nurplit/bambu-lights/data/Climbing_Dot.gif

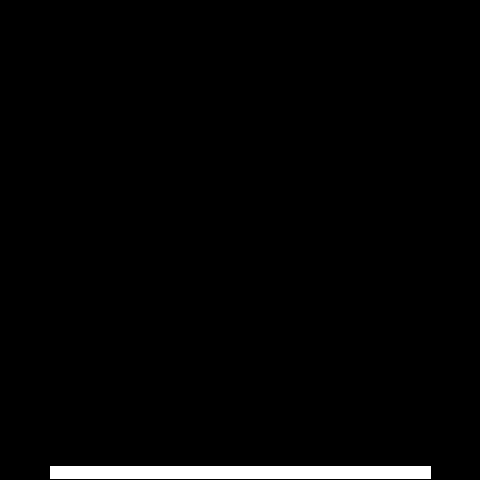
data/Climbing_Dot.gif
