nurplit/bambu-lights/data/Gradient_Fill.gif

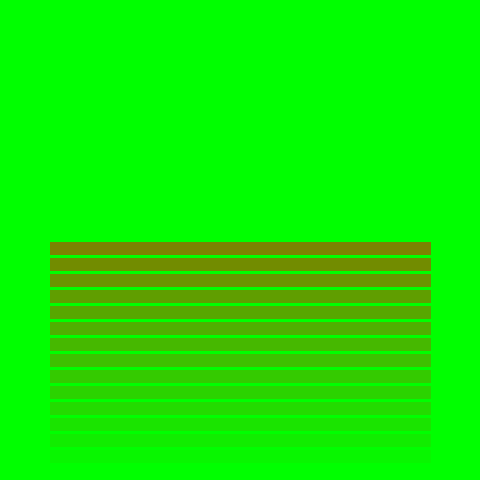
data/Gradient_Fill.gif
