nurplit/bambu-lights/src/main.cpp

/*
 * Bambu Lab Printer LED Controller
 * 
 * ESP32-based controller for addressable LED strips that displays the status
 * of Bambu Lab 3D printers via MQTT connection.
 * 
 * Inspired by and builds upon concepts from:
 * - BambuLights by judge2005 (https://github.com/judge2005/BambuLights)
 * 
 * Features:
 * - Web-based configuration interface
 * - OTA firmware updates
 * - Auto-off timer after print completion
 * - LiDAR pause support
 * - Door detection and automatic control
 * - Serial logging via web interface
 * - MQTT status monitoring
 * 
 * License: MIT
 * 
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
 * THE SOFTWARE IS PROVIDED "AS IS", WITHOUT WARRANTY OF ANY KIND, EXPRESS OR
 * IMPLIED, INCLUDING BUT NOT LIMITED TO THE WARRANTIES OF MERCHANTABILITY,
 * FITNESS FOR A PARTICULAR PURPOSE AND NONINFRINGEMENT. IN NO EVENT SHALL THE
 * AUTHORS OR COPYRIGHT HOLDERS BE LIABLE FOR ANY CLAIM, DAMAGES OR OTHER
 * LIABILITY, WHETHER IN AN ACTION OF CONTRACT, TORT OR OTHERWISE, ARISING FROM,
 * OUT OF OR IN CONNECTION WITH THE SOFTWARE OR THE USE OR OTHER DEALINGS IN THE
 * SOFTWARE.
 */

#include <Arduino.h>
#include <WiFi.h>
#include <WebServer.h>
#include <WiFiManager.h>
#include <espMqttClient.h>
#include <WiFiClientSecure.h>
#include <ArduinoJson.h>
#include <Preferences.h>
#include <ArduinoOTA.h>
#include <ESPmDNS.h>
#include <LittleFS.h>
#include "driver/rmt.h"
#include "esp_task_wdt.h"

// Custom header files
#include "config.h"
#include "structs.h"
#include "led_effects.h"
#include "printer_status.h"

// Configuration - Configurable via web interface
int led_pin = 2;                              // Default LED data pin
int num_leds = 10;                           // Default number of LEDs
String led_type = "WS2812B";                 // Default LED type
String color_order = "GRB";                  // Default color order
#define RMT_CHANNEL RMT_CHANNEL_0

// WiFi Configuration - Now handled by WiFiManager (no hardcoded credentials!)
const int WIFI_TIMEOUT_MS = 20000;           // 20 seconds timeout
WiFiManager wifiManager;                      // WiFiManager instance

// Bambu Lab MQTT Configuration - Configurable via web interface
String mqtt_server = "192.168.0.100";        // Default printer IP
int mqtt_port = 8883; // Use SSL port
const char* MQTT_USERNAME = "bblp";          // Default Bambu Lab username
String mqtt_password = "your_access_code";   // Configurable access code
String device_serial = "01S00A123456789";    // Configurable printer serial number
bool mqtt_use_ssl = true;                    // Use SSL/TLS for MQTT connection (port 8883)
bool mqtt_skip_cert_check = true;           // Skip SSL certificate verification (insecure but often needed)

// Home Assistant MQTT Configuration - Configurable via web interface
bool ha_mqtt_enabled = false;                // Enable/disable HA MQTT publishing
String ha_mqtt_server = "192.168.0.50";     // Home Assistant MQTT broker IP
int ha_mqtt_port = 1883;                    // HA MQTT broker port (usually 1883, non-SSL)
String ha_mqtt_username = "";               // HA MQTT username (empty if no auth)
String ha_mqtt_password = "";               // HA MQTT password (empty if no auth)
String ha_discovery_prefix = "homeassistant"; // HA discovery topic prefix
String ha_device_name = "Bambu Lights";     // Device name in Home Assistant
bool ha_mqtt_use_ssl = false;               // Usually false for local HA broker

// Preferences for storing settings
Preferences preferences;

// LED timing constants (in RMT ticks, 80MHz clock = 12.5ns per tick)
// Current timing values (will be set based on led_type)
int T0H = 32;   // 0 bit high time
int T0L = 64;   // 0 bit low time  
int T1H = 64;   // 1 bit high time
int T1L = 32;   // 1 bit low time

// Predefined timing for different LED types
struct LEDTiming {
    int t0h, t0l, t1h, t1l;
};

// LED type timing definitions (all in RMT ticks @ 80MHz)
const LEDTiming LED_TIMINGS[] = {
    // WS2812/WS2812B: T0H=0.4us, T0L=0.85us, T1H=0.8us, T1L=0.45us
    {32, 68, 64, 36},   // WS2812B
    // WS2811: T0H=0.5us, T0L=2.0us, T1H=1.2us, T1L=1.3us  
    {40, 160, 96, 104}, // WS2811
    // WS2813: Same as WS2812B but with backup data line
    {32, 68, 64, 36},   // WS2813
    // SK6812: T0H=0.3us, T0L=0.9us, T1H=0.6us, T1L=0.6us
    {24, 72, 48, 48},   // SK6812
    // APA102 uses SPI, but keeping for compatibility
    {32, 68, 64, 36}    // APA102 (fallback to WS2812 timing)
};

const String LED_TYPE_NAMES[] = {"WS2812B", "WS2811", "WS2813", "SK6812", "APA102"};
const String COLOR_ORDER_NAMES[] = {"RGB", "GRB", "BRG", "RBG", "GBR", "BGR"};

// Color structures (RGB defined in structs.h)
struct RGBW {
    uint8_t r, g, b, w;
};

// LED Array and RMT data (dynamically allocated in setup)
RGB* leds = nullptr;
RGBW* rgbw_leds = nullptr;
rmt_item32_t* led_data = nullptr;
bool is_rgbw = false; // Track if using RGBW LEDs

// Beacon LED Array (second strip for progress display)
RGB* beacon_leds = nullptr;
RGBW* beacon_rgbw_leds = nullptr;
rmt_item32_t* beacon_led_data = nullptr;
int beacon_led_count = DEFAULT_BEACON_LED_COUNT;
int beacon_led_pin = BEACON_LED_PIN;
int beacon_led_type = 0; // Default: WS2812B
int beacon_color_order = 1; // Default: GRB
bool beacon_enabled = false;
bool beacon_is_rgbw = false; // Track if beacon uses RGBW LEDs
String beacon_effect = "progress"; // progress, climbing, gradient, pulse
RGB beacon_color = {0, 255, 0}; // Default: green (start color for gradient)
int beacon_brightness = 80;
RGB beacon_climb_color = {255, 255, 255}; // Default: white for climbing pixel
int beacon_climb_speed = 150; // Milliseconds per step (default 150ms = 1.5s full cycle)
RGB beacon_gradient_end = {0, 0, 255}; // Default: blue for gradient end color
bool beacon_gradient_debug = false; // Flag to log gradient colors once per change
bool beacon_force_update = false; // Flag to force beacon render update

// Web Server and MQTT Client
WebServer server(80);

// Telnet Server for remote serial monitoring
WiFiServer telnetServer(23);  // Port 23 is standard for Telnet
WiFiClient telnetClient;
bool telnetConnected = false;

WiFiClient wifiClient;
WiFiClientSecure wifiClientSecure;
espMqttClientSecure mqttClient;  // Use secure client for SSL/TLS (Bambu printer)

// Home Assistant MQTT Client (separate connection)
espMqttClient haMqttClient(espMqttClientTypes::UseInternalTask::NO);

// Current mode tracking
enum LightMode {
    MODE_AUTO,      // Automatic color cycling
    MODE_MANUAL,    // Manual color control
    MODE_PRINTER,   // Bambu Lab printer status
    MODE_OFF        // LEDs off
};

LightMode currentMode = MODE_PRINTER;  // Default to Printer Status mode
RGB manualColor = {128, 0, 128}; // Default purple

// Auto-cycle fade variables
RGB currentAutoColor = {0, 0, 0};
RGB targetAutoColor = {0, 128, 0};
int fadeStep = 0;
int autoCycleSpeed = 50;  // Speed: 1-100 (higher = faster, affects FADE_STEPS)
int autoCycleBrightness = 100;  // Brightness: 0-100 (percentage)

// Printer status (struct defined in structs.h)
PrinterStatus printerStatus;

// Door event configuration
bool door_open_lights_enabled = false;
RGB door_open_color = {255, 255, 255}; // Default white for door open
bool door_is_open = false;
bool manual_door_trigger = false; // Manual override for firmware 01.10.00 bug
bool manual_beacon_trigger = false; // Manual override for beacon testing

// Timelapse configuration (uses MQTT credentials)
// printerIP comes from mqtt_server, accessCode from mqtt_password, serial from device_serial

// Auto-off timer configuration
int auto_off_minutes = 0; // 0 = disabled, otherwise minutes to wait after lights turn on
unsigned long lights_on_time = 0; // When did the lights turn on
bool auto_off_pending = false; // Is the timer running
LightMode mode_before_auto_off = MODE_PRINTER; // Remember mode to restore after auto-off

// Chamber light sync configuration
bool chamber_light_sync_enabled = true; // Sync chamber light with LED strip auto-off timer
bool chamber_light_was_on_before_auto_off = false; // Track chamber light state before auto-off

// LiDAR scanning configuration
bool lidar_lights_off_enabled = true; // Default: turn off lights during LiDAR scan
bool lidar_scanning = false;

// Printer Status LED Behavior Configuration (struct defined in structs.h)
PrinterStateBehavior behavior_heating = {"pulse", {255, 140, 0}, 70};        // Orange pulse during heating
PrinterStateBehavior behavior_printing = {"progress", {0, 255, 0}, 80};      // Green progress bar
PrinterStateBehavior behavior_idle = {"solid", {0, 0, 255}, 50};             // Blue solid
PrinterStateBehavior behavior_pause = {"solid", {255, 165, 0}, 70};          // Orange solid
PrinterStateBehavior behavior_finish = {"rainbow", {0, 0, 0}, 100};          // Rainbow cycle (color unused)
PrinterStateBehavior behavior_error = {"blink", {255, 0, 0}, 100};           // Red blink

// Track home_flag changes for debugging
long last_home_flag = 0;
bool home_flag_initialized = false;
int home_flag_update_count = 0; // Track number of updates to ensure fresh data

// MQTT Debug Logging
bool mqtt_full_logging = false; // Enable via web interface to log all MQTT traffic

// FINISH->IDLE transition control
bool idle_state_locked = false; // When true, prevent MQTT from overwriting IDLE state

// Beacon reinitialization deferred to main loop to avoid blocking web server
bool beacon_reinit_pending = false;
bool beacon_was_enabled_before_reinit = false;

// Timelapse detection
bool timelapse_active = false; // Track if timelapse is enabled for current print
bool timelapse_white_lights_enabled = true; // Force white lights during timelapse (default ON)

// Network scanning removed: user-configured manual setup via web UI is used instead.
// Keeping minimal placeholders for compatibility with older status displays.
bool scanInProgress = false;
String scanResult = "";

// Serial log buffer for web interface
#define SERIAL_LOG_SIZE 50
String serialLogs[SERIAL_LOG_SIZE];
int serialLogIndex = 0;
int serialLogCount = 0;

void addSerialLog(String msg) {
    serialLogs[serialLogIndex] = msg;
    serialLogIndex = (serialLogIndex + 1) % SERIAL_LOG_SIZE;
    if (serialLogCount < SERIAL_LOG_SIZE) {
        serialLogCount++;
    }
}

// Serial print that also logs to web interface and Telnet
void logPrint(String msg) {
    Serial.print(msg);
    addSerialLog(msg);
    // Send to Telnet client if connected
    if (telnetConnected && telnetClient && telnetClient.connected()) {
        telnetClient.print(msg);
    }
}

void logPrintln(String msg) {
    Serial.println(msg);
    addSerialLog(msg + "\n");
    // Send to Telnet client if connected
    if (telnetConnected && telnetClient && telnetClient.connected()) {
        telnetClient.println(msg);
    }
}

// Forward declarations
void updatePrinterLEDs();
void clearSettings();
void loadSettings();
void saveSettings();
bool testBambuMQTT(String ip);
void setAllLEDs(uint8_t r, uint8_t g, uint8_t b);
void clearAllLEDs();
void updateLEDs();
String listTimelapseFiles();
void publishHAState();
void publishHADiscovery();
bool connectHAMQTT();

void clearSettings() {
    preferences.begin("bambu", false);
    preferences.clear(); // Clear all saved settings
    preferences.end();
    Serial.println("EEPROM settings cleared - using defaults");
}

void loadSettings() {
    preferences.begin("bambu", false);
    mqtt_server = preferences.getString("mqtt_server", "192.168.0.100");
    mqtt_port = preferences.getInt("mqtt_port", 8883);  // Fixed default to SSL port
    mqtt_password = preferences.getString("mqtt_password", "your_access_code");
    device_serial = preferences.getString("device_serial", "01S00A123456789");
    mqtt_use_ssl = preferences.getBool("mqtt_use_ssl", true);  // Fixed default to SSL
    mqtt_skip_cert_check = preferences.getBool("mqtt_skip_cert", true);
    led_pin = preferences.getInt("led_pin", 2);
    num_leds = preferences.getInt("num_leds", 10);
    led_type = preferences.getString("led_type", "WS2812B");
    color_order = preferences.getString("color_order", "GRB");
    
    // Load door event configuration
    door_open_lights_enabled = preferences.getBool("door_lights", false);
    door_open_color.r = preferences.getUChar("door_r", 255);
    door_open_color.g = preferences.getUChar("door_g", 255);
    door_open_color.b = preferences.getUChar("door_b", 255);
    manual_door_trigger = preferences.getBool("door_trigger", false);
    // manual_beacon_trigger deliberately not loaded - always starts OFF to prevent continuous updates
    
    // Load LiDAR scanning configuration
    lidar_lights_off_enabled = preferences.getBool("lidar_lights_off", true);
    
    // Load auto-off timer configuration
    auto_off_minutes = preferences.getInt("auto_off_min", 0);
    
    // Load chamber light sync configuration
    chamber_light_sync_enabled = preferences.getBool("chamber_sync", true);
    Serial.println("Chamber Light Sync: " + String(chamber_light_sync_enabled ? "ENABLED" : "DISABLED"));
    
    // Load timelapse white lights configuration
    timelapse_white_lights_enabled = preferences.getBool("timelapse_white", true);
    Serial.println("Timelapse White Lights: " + String(timelapse_white_lights_enabled ? "ENABLED" : "DISABLED"));
    
    // Load printer status behavior settings
    behavior_heating.effect = preferences.getString("heat_effect", "pulse");
    behavior_heating.color.r = preferences.getUChar("heat_r", 255);
    behavior_heating.color.g = preferences.getUChar("heat_g", 140);
    behavior_heating.color.b = preferences.getUChar("heat_b", 0);
    behavior_heating.brightness = preferences.getInt("heat_bright", 70);
    
    behavior_printing.effect = preferences.getString("print_effect", "progress");
    behavior_printing.color.r = preferences.getUChar("print_r", 0);
    behavior_printing.color.g = preferences.getUChar("print_g", 255);
    behavior_printing.color.b = preferences.getUChar("print_b", 0);
    behavior_printing.brightness = preferences.getInt("print_bright", 80);
    
    behavior_idle.effect = preferences.getString("idle_effect", "solid");
    behavior_idle.color.r = preferences.getUChar("idle_r", 0);
    behavior_idle.color.g = preferences.getUChar("idle_g", 0);
    behavior_idle.color.b = preferences.getUChar("idle_b", 255);
    behavior_idle.brightness = preferences.getInt("idle_bright", 50);
    
    behavior_pause.effect = preferences.getString("pause_effect", "solid");
    behavior_pause.color.r = preferences.getUChar("pause_r", 255);
    behavior_pause.color.g = preferences.getUChar("pause_g", 165);
    behavior_pause.color.b = preferences.getUChar("pause_b", 0);
    behavior_pause.brightness = preferences.getInt("pause_bright", 70);
    
    behavior_finish.effect = preferences.getString("finish_effect", "rainbow");
    behavior_finish.color.r = preferences.getUChar("finish_r", 0);
    behavior_finish.color.g = preferences.getUChar("finish_g", 0);
    behavior_finish.color.b = preferences.getUChar("finish_b", 0);
    behavior_finish.brightness = preferences.getInt("finish_bright", 100);
    
    behavior_error.effect = preferences.getString("error_effect", "blink");
    behavior_error.color.r = preferences.getUChar("error_r", 255);
    behavior_error.color.g = preferences.getUChar("error_g", 0);
    behavior_error.color.b = preferences.getUChar("error_b", 0);
    behavior_error.brightness = preferences.getInt("error_bright", 100);
    
    // Load auto-cycle configuration
    autoCycleSpeed = preferences.getInt("cycle_speed", 50);
    autoCycleBrightness = preferences.getInt("cycle_bright", 100);
    
    // Load beacon LED configuration
    beacon_enabled = preferences.getBool("beacon_en", false);
    beacon_led_count = preferences.getInt("beacon_count", DEFAULT_BEACON_LED_COUNT);
    beacon_led_pin = preferences.getInt("beacon_pin", BEACON_LED_PIN);
    beacon_led_type = preferences.getInt("beacon_type", 0); // 0 = WS2812B
    beacon_color_order = preferences.getInt("beacon_order", 1); // 1 = GRB
    beacon_is_rgbw = preferences.getBool("beacon_rgbw", false); // RGB by default
    beacon_effect = preferences.getString("beacon_fx", "progress");
    beacon_color.r = preferences.getUChar("beacon_r", 0);
    beacon_color.g = preferences.getUChar("beacon_g", 255);
    beacon_color.b = preferences.getUChar("beacon_b", 0);
    beacon_brightness = preferences.getInt("beacon_bright", 80);
    beacon_climb_color.r = preferences.getUChar("beacon_climb_r", 255);
    beacon_climb_color.g = preferences.getUChar("beacon_climb_g", 255);
    beacon_climb_color.b = preferences.getUChar("beacon_climb_b", 255);
    beacon_climb_speed = preferences.getInt("bcn_clmb_spd", 150);
    beacon_gradient_end.r = preferences.getUChar("bcn_grad_end_r", 0);
    beacon_gradient_end.g = preferences.getUChar("bcn_grad_end_g", 0);
    beacon_gradient_end.b = preferences.getUChar("bcn_grad_end_b", 255);
    
    Serial.printf("Loaded beacon climb speed: %d ms\n", beacon_climb_speed);
    Serial.printf("Loaded beacon climb color: R=%d G=%d B=%d\n", beacon_climb_color.r, beacon_climb_color.g, beacon_climb_color.b);
    Serial.printf("Loaded beacon gradient end: R=%d G=%d B=%d\n", beacon_gradient_end.r, beacon_gradient_end.g, beacon_gradient_end.b);
    
    // Load Home Assistant MQTT configuration
    ha_mqtt_enabled = preferences.getBool("ha_mqtt_en", false);
    ha_mqtt_server = preferences.getString("ha_mqtt_srv", "192.168.0.50");
    ha_mqtt_port = preferences.getInt("ha_mqtt_port", 1883);
    ha_mqtt_username = preferences.getString("ha_mqtt_user", "");
    ha_mqtt_password = preferences.getString("ha_mqtt_pass", "");
    ha_discovery_prefix = preferences.getString("ha_disc_pfx", "homeassistant");
    ha_device_name = preferences.getString("ha_dev_name", "Bambu Lights");
    ha_mqtt_use_ssl = preferences.getBool("ha_mqtt_ssl", false);
    
    preferences.end();
    
    Serial.println("Settings loaded:");
    Serial.printf("MQTT Server: %s\n", mqtt_server.c_str());
    Serial.printf("MQTT Port: %d (SSL: %s)\n", mqtt_port, mqtt_use_ssl ? "YES" : "NO");
    Serial.printf("Device Serial: %s\n", device_serial.c_str());
    Serial.printf("LED Pin: %d, Count: %d\n", led_pin, num_leds);
    Serial.printf("Beacon: %s, Pin: %d, Count: %d\n", beacon_enabled ? "ENABLED" : "DISABLED", beacon_led_pin, beacon_led_count);
    Serial.printf("Door Lights: %s\n", door_open_lights_enabled ? "ENABLED" : "DISABLED");
    Serial.printf("LiDAR Lights Off: %s\n", lidar_lights_off_enabled ? "ENABLED" : "DISABLED");
    Serial.printf("Home Assistant MQTT: %s\n", ha_mqtt_enabled ? "ENABLED" : "DISABLED");
    if (ha_mqtt_enabled) {
        Serial.printf("  HA Broker: %s:%d\n", ha_mqtt_server.c_str(), ha_mqtt_port);
    }
    Serial.println("MQTT Password: [HIDDEN]");
}

void saveSettings() {
    preferences.begin("bambu", false);
    preferences.putString("mqtt_server", mqtt_server);
    preferences.putInt("mqtt_port", mqtt_port);
    preferences.putString("mqtt_password", mqtt_password);
    preferences.putString("device_serial", device_serial);
    preferences.putBool("mqtt_use_ssl", mqtt_use_ssl);
    preferences.putBool("mqtt_skip_cert", mqtt_skip_cert_check);
    preferences.putInt("led_pin", led_pin);
    preferences.putInt("num_leds", num_leds);
    preferences.putString("led_type", led_type);
    preferences.putString("color_order", color_order);
    
    // Save door event configuration
    preferences.putBool("door_lights", door_open_lights_enabled);
    preferences.putUChar("door_r", door_open_color.r);
    preferences.putUChar("door_g", door_open_color.g);
    preferences.putUChar("door_b", door_open_color.b);
    
    // Save LiDAR scanning configuration
    preferences.putBool("lidar_lights_off", lidar_lights_off_enabled);
    
    // Save chamber light sync configuration
    preferences.putBool("chamber_sync", chamber_light_sync_enabled);
    
    // Save timelapse white lights configuration
    preferences.putBool("timelapse_white", timelapse_white_lights_enabled);
    
    // Save auto-cycle configuration
    preferences.putInt("cycle_speed", autoCycleSpeed);
    preferences.putInt("cycle_bright", autoCycleBrightness);
    
    // Save beacon LED configuration
    preferences.putBool("beacon_en", beacon_enabled);
    preferences.putInt("beacon_count", beacon_led_count);
    preferences.putInt("beacon_pin", beacon_led_pin);
    preferences.putInt("beacon_type", beacon_led_type);
    preferences.putInt("beacon_order", beacon_color_order);
    preferences.putBool("beacon_rgbw", beacon_is_rgbw);
    preferences.putString("beacon_fx", beacon_effect);
    preferences.putUChar("beacon_r", beacon_color.r);
    preferences.putUChar("beacon_g", beacon_color.g);
    preferences.putUChar("beacon_b", beacon_color.b);
    preferences.putInt("beacon_bright", beacon_brightness);
    preferences.putUChar("beacon_climb_r", beacon_climb_color.r);
    preferences.putUChar("beacon_climb_g", beacon_climb_color.g);
    preferences.putUChar("beacon_climb_b", beacon_climb_color.b);
    preferences.putInt("bcn_clmb_spd", beacon_climb_speed);
    preferences.putUChar("bcn_grad_end_r", beacon_gradient_end.r);
    preferences.putUChar("bcn_grad_end_g", beacon_gradient_end.g);
    preferences.putUChar("bcn_grad_end_b", beacon_gradient_end.b);
    
    // Save Home Assistant MQTT configuration
    preferences.putBool("ha_mqtt_en", ha_mqtt_enabled);
    preferences.putString("ha_mqtt_srv", ha_mqtt_server);
    preferences.putInt("ha_mqtt_port", ha_mqtt_port);
    preferences.putString("ha_mqtt_user", ha_mqtt_username);
    preferences.putString("ha_mqtt_pass", ha_mqtt_password);
    preferences.putString("ha_disc_pfx", ha_discovery_prefix);
    preferences.putString("ha_dev_name", ha_device_name);
    preferences.putBool("ha_mqtt_ssl", ha_mqtt_use_ssl);
    
    preferences.end();
    
    Serial.println("Configuration saved to EEPROM");
}

bool testBambuMQTT(String ip) {
    Serial.printf("Testing MQTT connection to %s:%d\n", ip.c_str(), mqtt_port);
    Serial.println("Note: Using simplified test - espMqttClient conversion complete");
    
    // Simplified test - just return true since we know it's a Bambu printer
    // The full test would require setting up another espMqttClient instance
    return true; // Assume Bambu printer if IP scanning reached this point
}

// Network scanning functions removed. Manual configuration via web UI is now the supported flow.

void configureLEDTiming() {
    // Find the LED type index
    int typeIndex = 0; // Default to WS2812B
    for (int i = 0; i < 5; i++) {
        if (led_type == LED_TYPE_NAMES[i]) {
            typeIndex = i;
            break;
        }
    }
    
    // Set timing values
    T0H = LED_TIMINGS[typeIndex].t0h;
    T0L = LED_TIMINGS[typeIndex].t0l;
    T1H = LED_TIMINGS[typeIndex].t1h;
    T1L = LED_TIMINGS[typeIndex].t1l;
    
    // Check if this is an RGBW LED type
    is_rgbw = (led_type == "SK6812");
    
    // LED timing configured
}

uint32_t applyColorOrder(RGB color, uint8_t white = 0) {
    if (is_rgbw) {
        // For RGBW LEDs (SK6812), return 32-bit value with white channel
        // SK6812 standard order is GRBW (Green, Red, Blue, White)
        if (color_order == "RGBW") {
            return (color.r << 24) | (color.g << 16) | (color.b << 8) | white;
        } else if (color_order == "GRBW" || color_order == "GRB") {
            // GRB maps to GRBW for SK6812
            return (color.g << 24) | (color.r << 16) | (color.b << 8) | white;
        } else if (color_order == "RGB") {
            // RGB maps to RGBW
            return (color.r << 24) | (color.g << 16) | (color.b << 8) | white;
        } else {
            // Default: GRBW (standard SK6812 order)
            return (color.g << 24) | (color.r << 16) | (color.b << 8) | white;
        }
    } else {
        // For RGB LEDs, return 24-bit value
        if (color_order == "RGB") {
            return (color.r << 16) | (color.g << 8) | color.b;
        } else if (color_order == "GRB") {
            return (color.g << 16) | (color.r << 8) | color.b;
        } else if (color_order == "BRG") {
            return (color.b << 16) | (color.r << 8) | color.g;
        } else if (color_order == "RBG") {
            return (color.r << 16) | (color.b << 8) | color.g;
        } else if (color_order == "GBR") {
            return (color.g << 16) | (color.b << 8) | color.r;
        } else if (color_order == "BGR") {
            return (color.b << 16) | (color.g << 8) | color.r;
        }
        // Default to GRB if unknown
        return (color.g << 16) | (color.r << 8) | color.b;
    }
}

void setupRMT() {
    rmt_config_t config = {};
    config.rmt_mode = RMT_MODE_TX;
    config.channel = RMT_CHANNEL;
    config.gpio_num = (gpio_num_t)led_pin;
    config.mem_block_num = 1;
    config.clk_div = 1; // 80MHz clock
    config.tx_config.loop_en = false;
    config.tx_config.carrier_en = false;
    config.tx_config.idle_level = RMT_IDLE_LEVEL_LOW;
    config.tx_config.idle_output_en = true;
    
    ESP_ERROR_CHECK(rmt_config(&config));
    ESP_ERROR_CHECK(rmt_driver_install(config.channel, 0, 0));
}

void rgbToRMT(RGB* colors, rmt_item32_t* items, int numLeds, RGBW* rgbw_colors = nullptr) {
    int idx = 0;
    int bitsPerLed = is_rgbw ? 32 : 24; // RGBW uses 32 bits, RGB uses 24 bits
    
    for (int led = 0; led < numLeds; led++) {
        uint32_t color;
        if (is_rgbw && rgbw_colors) {
            // Use RGBW data
            RGB rgb_part = {rgbw_colors[led].r, rgbw_colors[led].g, rgbw_colors[led].b};
            color = applyColorOrder(rgb_part, rgbw_colors[led].w);
        } else {
            // Use RGB data
            color = applyColorOrder(colors[led]);
        }
        
        for (int bit = bitsPerLed - 1; bit >= 0; bit--) {
            if (color & (1UL << bit)) {
                // Send '1'
                items[idx].level0 = 1;
                items[idx].duration0 = T1H;
                items[idx].level1 = 0; 
                items[idx].duration1 = T1L;
            } else {
                // Send '0'
                items[idx].level0 = 1;
                items[idx].duration0 = T0H;
                items[idx].level1 = 0;
                items[idx].duration1 = T0L;
            }
            idx++;
        }
    }
}

void updateLEDs() {
    if (led_data) {
        if (is_rgbw && rgbw_leds) {
            rgbToRMT(nullptr, led_data, num_leds, rgbw_leds);
        } else if (leds) {
            rgbToRMT(leds, led_data, num_leds);
        }
        int bitsPerLed = is_rgbw ? 32 : 24;
        ESP_ERROR_CHECK(rmt_write_items(RMT_CHANNEL, led_data, num_leds * bitsPerLed, true));
    }
}

void setLED(int index, uint8_t r, uint8_t g, uint8_t b, uint8_t w = 0) {
    if (index >= 0 && index < num_leds) {
        if (is_rgbw && rgbw_leds) {
            // For RGBW LEDs, optimize pure white by using the white channel
            if (w == 0 && r > 0 && r == g && g == b) {
                // RGB values are equal (gray/white) - use white channel instead
                rgbw_leds[index].r = 0;
                rgbw_leds[index].g = 0;
                rgbw_leds[index].b = 0;
                rgbw_leds[index].w = r;  // Move the brightness to white channel
            } else {
                rgbw_leds[index].r = r;
                rgbw_leds[index].g = g;
                rgbw_leds[index].b = b;
                rgbw_leds[index].w = w;
            }
        } else if (leds) {
            leds[index].r = r;
            leds[index].g = g;
            leds[index].b = b;
        }
    }
}

void setAllLEDs(uint8_t r, uint8_t g, uint8_t b) {
    for (int i = 0; i < num_leds; i++) {
        setLED(i, r, g, b);
    }
}

void clearAllLEDs() {
    setAllLEDs(0, 0, 0);
}

void reallocateLEDs() {
    // Clean up existing arrays
    if (leds) {
        delete[] leds;
        leds = nullptr;
    }
    if (rgbw_leds) {
        delete[] rgbw_leds;
        rgbw_leds = nullptr;
    }
    if (led_data) {
        delete[] led_data;
        led_data = nullptr;
    }
    
    // Allocate new arrays with current num_leds
    if (num_leds > 0) {
        // Allocate RGB or RGBW array based on LED type
        if (is_rgbw) {
            rgbw_leds = new RGBW[num_leds];
            // Initialize all LEDs to off
            for (int i = 0; i < num_leds; i++) {
                rgbw_leds[i] = {0, 0, 0, 0};
            }
        } else {
            leds = new RGB[num_leds];
            // Initialize all LEDs to off
            for (int i = 0; i < num_leds; i++) {
                leds[i] = {0, 0, 0};
            }
        }
        
        // Allocate RMT data: 24 bits for RGB, 32 bits for RGBW
        int bitsPerLed = is_rgbw ? 32 : 24;
        led_data = new rmt_item32_t[num_leds * bitsPerLed];
        
        // RMT data allocated
    }
}

// ==================== BEACON LED FUNCTIONS ====================

void configureBeaconTiming() {
    // Beacon uses same timing as main LEDs, just stored separately
    // Get timing from beacon_led_type (0-4 index)
    if (beacon_led_type >= 0 && beacon_led_type < 5) {
        // Timing is already configured via LED_TIMINGS array
        // Individual beacon will use these when rendering
    }
}

void setupBeaconRMT() {
    if (!beacon_enabled || beacon_led_count <= 0) return;
    
    // Use RMT_CHANNEL_1 for beacon (main LEDs use RMT_CHANNEL_0)
    rmt_config_t config = {};
    config.rmt_mode = RMT_MODE_TX;
    config.channel = RMT_CHANNEL_1;
    config.gpio_num = (gpio_num_t)beacon_led_pin;
    config.mem_block_num = 1;
    config.clk_div = 1; // 80MHz clock
    config.tx_config.loop_en = false;
    config.tx_config.carrier_en = false;
    config.tx_config.idle_level = RMT_IDLE_LEVEL_LOW;
    config.tx_config.idle_output_en = true;
    
    esp_err_t err = rmt_config(&config);
    if (err == ESP_OK) {
        err = rmt_driver_install(config.channel, 0, 0);
        if (err == ESP_OK) {
            Serial.printf("Beacon RMT configured on GPIO %d, Channel 1\n", beacon_led_pin);
        } else {
            Serial.printf("Beacon RMT driver install failed: %d\n", err);
            beacon_enabled = false;
        }
    } else {
        Serial.printf("Beacon RMT config failed: %d\n", err);
        beacon_enabled = false;
    }
}

uint32_t applyBeaconColorOrder(RGB color) {
    // Apply color order for beacon LEDs
    switch (beacon_color_order) {
        case 0: return (color.r << 16) | (color.g << 8) | color.b; // RGB
        case 1: return (color.g << 16) | (color.r << 8) | color.b; // GRB
        case 2: return (color.b << 16) | (color.r << 8) | color.g; // BRG
        case 3: return (color.r << 16) | (color.b << 8) | color.g; // RBG
        case 4: return (color.g << 16) | (color.b << 8) | color.r; // GBR
        case 5: return (color.b << 16) | (color.g << 8) | color.r; // BGR
        default: return (color.g << 16) | (color.r << 8) | color.b; // Default GRB
    }
}

void beaconRgbToRMT(RGB* colors, rmt_item32_t* items, int numLeds) {
    int idx = 0;
    const LEDTiming& timing = LED_TIMINGS[beacon_led_type];
    int bitsPerLed = beacon_is_rgbw ? 32 : 24;
    
    for (int led = 0; led < numLeds; led++) {
        uint32_t color;
        if (beacon_is_rgbw && beacon_rgbw_leds) {
            // RGBW: send all 4 channels
            RGBW rgbw = beacon_rgbw_leds[led];
            switch (beacon_color_order) {
                case 0: color = ((uint32_t)rgbw.r << 24) | ((uint32_t)rgbw.g << 16) | ((uint32_t)rgbw.b << 8) | rgbw.w; break; // RGBW
                case 1: color = ((uint32_t)rgbw.g << 24) | ((uint32_t)rgbw.r << 16) | ((uint32_t)rgbw.b << 8) | rgbw.w; break; // GRBW
                case 2: color = ((uint32_t)rgbw.b << 24) | ((uint32_t)rgbw.r << 16) | ((uint32_t)rgbw.g << 8) | rgbw.w; break; // BRGW
                case 3: color = ((uint32_t)rgbw.r << 24) | ((uint32_t)rgbw.b << 16) | ((uint32_t)rgbw.g << 8) | rgbw.w; break; // RBGW
                case 4: color = ((uint32_t)rgbw.g << 24) | ((uint32_t)rgbw.b << 16) | ((uint32_t)rgbw.r << 8) | rgbw.w; break; // GBRW
                case 5: color = ((uint32_t)rgbw.b << 24) | ((uint32_t)rgbw.g << 16) | ((uint32_t)rgbw.r << 8) | rgbw.w; break; // BGRW
                default: color = ((uint32_t)rgbw.g << 24) | ((uint32_t)rgbw.r << 16) | ((uint32_t)rgbw.b << 8) | rgbw.w; break; // Default GRBW
            }
        } else {
            // RGB: send 3 channels
            color = applyBeaconColorOrder(colors[led]);
        }
        
        for (int bit = bitsPerLed - 1; bit >= 0; bit--) {
            if (color & (1UL << bit)) {
                items[idx].level0 = 1;
                items[idx].duration0 = timing.t1h;
                items[idx].level1 = 0;
                items[idx].duration1 = timing.t1l;
            } else {
                items[idx].level0 = 1;
                items[idx].duration0 = timing.t0h;
                items[idx].level1 = 0;
                items[idx].duration1 = timing.t0l;
            }
            idx++;
        }
    }
}

void updateBeaconLEDs() {
    if (!beacon_enabled || !beacon_leds || !beacon_led_data || beacon_led_count <= 0) {
        return;
    }
    
    // Convert LED data to RMT format
    beaconRgbToRMT(beacon_leds, beacon_led_data, beacon_led_count);
    
    // Write to RMT with NON-BLOCKING mode (wait=false) to prevent web server stalls
    // This is critical - blocking RMT writes were causing the web lockups
    int bitsPerLed = beacon_is_rgbw ? 32 : 24;
    esp_err_t err = rmt_write_items(RMT_CHANNEL_1, beacon_led_data, beacon_led_count * bitsPerLed, false);
    if (err != ESP_OK) {
        // Silently fail - don't block on errors
    }
}

void setBeaconLED(int index, uint8_t r, uint8_t g, uint8_t b) {
    if (index >= 0 && index < beacon_led_count && beacon_leds) {
        // Always set RGB values in beacon_leds (used as staging)
        beacon_leds[index].r = r;
        beacon_leds[index].g = g;
        beacon_leds[index].b = b;
        
        // Also set RGBW array if in RGBW mode
        if (beacon_is_rgbw && beacon_rgbw_leds) {
            beacon_rgbw_leds[index].r = r;
            beacon_rgbw_leds[index].g = g;
            beacon_rgbw_leds[index].b = b;
            beacon_rgbw_leds[index].w = 0; // No white channel for color LEDs
        }
    }
}

void clearBeaconLEDs() {
    for (int i = 0; i < beacon_led_count; i++) {
        setBeaconLED(i, 0, 0, 0);
    }
}

void reallocateBeaconLEDs() {
    // Clean up existing arrays
    if (beacon_leds) {
        delete[] beacon_leds;
        beacon_leds = nullptr;
    }
    if (beacon_rgbw_leds) {
        delete[] beacon_rgbw_leds;
        beacon_rgbw_leds = nullptr;
    }
    if (beacon_led_data) {
        delete[] beacon_led_data;
        beacon_led_data = nullptr;
    }
    
    // Allocate new arrays if enabled
    if (beacon_enabled && beacon_led_count > 0) {
        int bitsPerLed = beacon_is_rgbw ? 32 : 24;
        
        // Always allocate beacon_leds as staging array for RGB values
        beacon_leds = new RGB[beacon_led_count];
        for (int i = 0; i < beacon_led_count; i++) {
            beacon_leds[i] = {0, 0, 0};
        }
        
        // Additionally allocate RGBW array if needed
        if (beacon_is_rgbw) {
            beacon_rgbw_leds = new RGBW[beacon_led_count];
            for (int i = 0; i < beacon_led_count; i++) {
                beacon_rgbw_leds[i] = {0, 0, 0, 0};
            }
        }
        
        beacon_led_data = new rmt_item32_t[beacon_led_count * bitsPerLed];
        
        Serial.printf("Beacon LEDs allocated: %d LEDs (%s)\n", beacon_led_count, beacon_is_rgbw ? "RGBW" : "RGB");
    }
}

void updateBeaconProgress(int progress) {
    if (!beacon_enabled || !beacon_leds) return;
    
    // Manual override: force beacon on with current effect at 100%
    if (manual_beacon_trigger) {
        progress = 100;
    }
    
    // Skip update if progress hasn't changed (reduces CPU load significantly)
    // Exception: "progress" effect always updates for animation, or force update flag is set
    static int lastProgress = -1;
    static String lastEffect = "";
    if (progress == lastProgress && beacon_effect == lastEffect && beacon_effect != "progress" && !beacon_force_update) {
        return; // No change, skip expensive update
    }
    beacon_force_update = false; // Clear force update flag
    lastProgress = progress;
    lastEffect = beacon_effect;
    
    // Calculate brightness-adjusted color
    uint8_t r = (beacon_color.r * beacon_brightness) / 100;
    uint8_t g = (beacon_color.g * beacon_brightness) / 100;
    uint8_t b = (beacon_color.b * beacon_brightness) / 100;
    
    if (beacon_effect == "progress") {
        // Progress bar: fill from bottom to top with animated white climbing pixel
        int litLEDs = (progress * beacon_led_count) / 100;
        
        // Animated climbing pixel (continuously climbs from bottom to top)
        static unsigned long lastClimbUpdate = 0;
        static int climbPosition = 0;
        
        if (millis() - lastClimbUpdate > beacon_climb_speed) {
            lastClimbUpdate = millis();
            climbPosition++;
            if (climbPosition >= beacon_led_count) {
                climbPosition = 0; // Reset to bottom when reaching top
            }
        }
        
        // Draw progress bar
        for (int i = 0; i < beacon_led_count; i++) {
            if (i == climbPosition) {
                // Climbing pixel with custom color (always visible)
                setBeaconLED(i, beacon_climb_color.r, beacon_climb_color.g, beacon_climb_color.b);
            } else if (i < litLEDs) {
                // Normal progress color
                setBeaconLED(i, r, g, b);
            } else {
                // Off
                setBeaconLED(i, 0, 0, 0);
            }
        }
    } else if (beacon_effect == "climbing") {
        // Climbing dot: single LED moves up
        clearBeaconLEDs();
        int ledIndex = (progress * (beacon_led_count - 1)) / 100;
        setBeaconLED(ledIndex, r, g, b);
    } else if (beacon_effect == "gradient") {
        // Gradient fill: transitions from start color to end color as it fills
        uint8_t end_r = (beacon_gradient_end.r * beacon_brightness) / 100;
        uint8_t end_g = (beacon_gradient_end.g * beacon_brightness) / 100;
        uint8_t end_b = (beacon_gradient_end.b * beacon_brightness) / 100;
        
        // Log gradient colors once per change
        if (beacon_gradient_debug) {
            logPrintln("Rendering gradient: Start RGB(" + String(r) + "," + String(g) + "," + String(b) + ") -> End RGB(" + String(end_r) + "," + String(end_g) + "," + String(end_b) + ") Progress=" + String(progress) + "%");
            beacon_gradient_debug = false;
        }
        
        int litLEDs = (progress * beacon_led_count) / 100;
        for (int i = 0; i < beacon_led_count; i++) {
            if (i < litLEDs) {
                // Smooth gradient from start color (bottom) to end color (top)
                int blend = (i * 100) / max(1, litLEDs - 1);
                uint8_t grad_r = r + ((end_r - r) * blend) / 100;
                uint8_t grad_g = g + ((end_g - g) * blend) / 100;
                uint8_t grad_b = b + ((end_b - b) * blend) / 100;
                setBeaconLED(i, grad_r, grad_g, grad_b);
            } else {
                setBeaconLED(i, 0, 0, 0);
            }
        }
    } else if (beacon_effect == "pulse") {
        // Pulse: all LEDs pulse together (simplified for better performance)
        // Fill up to current progress level with pulsing brightness
        static unsigned long lastPulseCalc = 0;
        static int pulseBright = beacon_brightness;
        
        // Only recalculate pulse brightness every 100ms (was 50ms)
        if (millis() - lastPulseCalc > 100) {
            static int pulseDir = 1;
            pulseBright += pulseDir * 15;
            if (pulseBright >= beacon_brightness) {
                pulseBright = beacon_brightness;
                pulseDir = -1;
            } else if (pulseBright <= beacon_brightness / 3) {
                pulseBright = beacon_brightness / 3;
                pulseDir = 1;
            }
            lastPulseCalc = millis();
        }
        
        uint8_t pulse_r = (beacon_color.r * pulseBright) / 100;
        uint8_t pulse_g = (beacon_color.g * pulseBright) / 100;
        uint8_t pulse_b = (beacon_color.b * pulseBright) / 100;
        
        int litLEDs = (progress * beacon_led_count) / 100;
        for (int i = 0; i < beacon_led_count; i++) {
            if (i < litLEDs) {
                setBeaconLED(i, pulse_r, pulse_g, pulse_b);
            } else {
                setBeaconLED(i, 0, 0, 0);
            }
        }
    }
    
    updateBeaconLEDs();
}

// ==================== END BEACON LED FUNCTIONS ====================

bool connectWiFi() {
    logPrintln("Starting WiFi connection...");
    
    // Set blue color while connecting
    setAllLEDs(0, 0, 255);
    updateLEDs();
    
    WiFi.mode(WIFI_STA);
    
    // WiFiManager will handle the connection
    // If no saved credentials, it will start an Access Point
    wifiManager.setConfigPortalTimeout(180); // 3 minutes timeout for config portal
    wifiManager.setConnectTimeout(20);       // 20 seconds to connect to saved WiFi
    
    // Create unique AP name based on chip ID
    String apName = "BambuLED-" + String((uint32_t)ESP.getEfuseMac(), HEX);
    logPrintln("AP Name (if needed): " + apName);
    logPrintln("If no WiFi configured, connect to AP and visit 192.168.4.1");
    
    // Blink blue while connecting
    bool ledState = false;
    wifiManager.setAPCallback([](WiFiManager *myWiFiManager) {
        Serial.println("Entered config mode - AP started");
        Serial.println("Connect to: " + String(myWiFiManager->getConfigPortalSSID()));
        Serial.println("Visit: 192.168.4.1 to configure WiFi");
    });
    
    // Try to connect with saved credentials or start config portal
    bool connected = wifiManager.autoConnect(apName.c_str());
    
    if (connected) {
        logPrintln("WiFi connected! IP: " + WiFi.localIP().toString());
        logPrintln("Signal strength: " + String(WiFi.RSSI()) + " dBm");
        
        // Green color for successful connection
        setAllLEDs(0, 255, 0);
        updateLEDs();
        delay(2000);
        
        return true;
    } else {
        logPrintln("WiFi connection failed or timed out!");
        
        // Red color for failed connection
        setAllLEDs(255, 0, 0);
        updateLEDs();
        delay(2000);
        
        return false;
    }
}

// MQTT Functions
static unsigned long messageCount = 0;
static String assembledMessage = "";
static String assembledTopic = "";

// Forward declaration
void processMqttMessage(const String& topic, const String& message);

// Send MQTT command to printer
void sendPrinterCommand(const String& command) {
    if (!mqttClient.connected()) {
        logPrintln("Cannot send command - MQTT not connected");
        return;
    }
    
    String requestTopic = "device/" + device_serial + "/request";
    logPrintln("Sending MQTT command to: " + requestTopic);
    logPrintln("Command: " + command);
    
    mqttClient.publish(requestTopic.c_str(), 0, false, command.c_str());
}

// Control chamber light (on/off with optional brightness)
void setChamberLight(bool on, int brightness = 100) {
    // Track last command to avoid flooding MQTT with redundant messages
    static bool last_state = false;
    static unsigned long last_command_time = 0;
    static uint32_t seq_id = 1;
    unsigned long now = millis();
    
    // Only send if state changed OR it's been more than 5 seconds (for reliability)
    if (on == last_state && (now - last_command_time < 5000)) {
        return; // Skip redundant command
    }
    
    last_state = on;
    last_command_time = now;
    
    // Try direct LED mode control for chamber light
    // Mode: "on" or "off" for chamber light control
    String command = "{\"system\":{\"sequence_id\":\"" + String(seq_id++) + 
                     "\",\"command\":\"ledctrl\",\"led_node\":\"chamber_light\",\"led_mode\":\"";
    command += on ? "on" : "off";
    command += "\",\"led_on_time\":500,\"led_off_time\":500,\"loop_times\":1,\"interval_time\":0}}";
    
    sendPrinterCommand(command);
    logPrintln("Chamber light: " + String(on ? "ON" : "OFF") + " (LED control: " + String(on ? "on" : "off") + ")");
}

void onMqttMessage(const espMqttClientTypes::MessageProperties& properties, const char* topic, const uint8_t* payload, size_t len, size_t index, size_t total) {
    // Handle message assembly for multi-part messages
    if (index == 0) {
        // Start of new message
        messageCount++;
        assembledMessage = "";
        assembledTopic = String(topic);
        if (messageCount % 10 == 1) { // Log every 10th message to web
            logPrintln("MQTT message #" + String(messageCount) + " (" + String(total) + " bytes)");
        }
    }
    
    // Append this part to the assembled message
    for (size_t i = 0; i < len; i++) {
        assembledMessage += (char)payload[i];
    }
    
    // Only process when we have the complete message (index + len == total)
    if (index + len >= total) {

        
        processMqttMessage(assembledTopic, assembledMessage);
    }
}

void processMqttMessage(const String& topic, const String& message) {
    // Throttle message processing to avoid blocking web server
    static unsigned long lastProcessTime = 0;
    unsigned long now = millis();
    
    // Process at most once per 100ms to keep web responsive
    if (now - lastProcessTime < 100) {
        return; // Skip this message, too soon after last one
    }
    lastProcessTime = now;
    
    yield(); // Yield before heavy processing
    
    // Full MQTT logging if enabled
    if (mqtt_full_logging) {
        logPrintln("========== MQTT MESSAGE ==========");
        logPrintln("Topic: " + topic);
        logPrintln("Size: " + String(message.length()) + " bytes");
        logPrintln("Payload: " + message);
        logPrintln("==================================");
    }
    
    // Parse JSON message - 20KB buffer needed for large Bambu Lab messages
    DynamicJsonDocument doc(20480); // 20KB buffer for 15.6KB messages
    DeserializationError error = deserializeJson(doc, message);
    
    yield(); // Yield after heavy JSON parsing
    
    if (error) {
        Serial.printf("JSON error: %s\n", error.c_str());
        return;
    }
    
    // Update printer status
    printerStatus.online = true;
    printerStatus.lastUpdate = millis();
    
    // Log key fields for debugging (always enabled for state tracking)
    if (doc.containsKey("print")) {
        JsonObject print = doc["print"];
        String debugInfo = "MQTT Update: ";
        
        if (print.containsKey("gcode_state")) {
            debugInfo += "State=" + print["gcode_state"].as<String>() + " ";
        }
        if (print.containsKey("mc_print_stage")) {
            debugInfo += "Stage=" + print["mc_print_stage"].as<String>() + " ";
        }
        if (print.containsKey("stg_cur")) {
            debugInfo += "StgNum=" + String(print["stg_cur"].as<int>()) + " ";
        }
        if (print.containsKey("mc_percent")) {
            debugInfo += "Progress=" + String(print["mc_percent"].as<int>()) + "% ";
        }
        if (print.containsKey("layer_num")) {
            debugInfo += "Layer=" + String(print["layer_num"].as<int>());
            if (print.containsKey("total_layer_num")) {
                debugInfo += "/" + String(print["total_layer_num"].as<int>());
            }
            debugInfo += " ";
        }
        if (print.containsKey("bed_temper")) {
            debugInfo += "Bed=" + String(print["bed_temper"].as<float>(), 1) + "C ";
        }
        if (print.containsKey("nozzle_temper")) {
            debugInfo += "Nozzle=" + String(print["nozzle_temper"].as<float>(), 1) + "C ";
        }
        
        // Only show error code if non-zero (indicates actual error)
        if (print.containsKey("print_error")) {
            int error_code = print["print_error"].as<int>();
            if (error_code != 0) {
                debugInfo += "Error=" + String(error_code) + " ";
            }
        }
        
        if (debugInfo.length() > 13) { // More than just "MQTT Update: "
            logPrintln(debugInfo);
        }
    }
    
    if (doc.containsKey("print")) {
        JsonObject print = doc["print"];
        
        // Parse stage - try multiple field names
        if (print.containsKey("stg_cur")) {
            // stg_cur is the actual stage number (more reliable)
            int stage_num = print["stg_cur"];
            printerStatus.stage = String(stage_num);
        } else if (print.containsKey("stage")) {
            printerStatus.stage = print["stage"].as<String>();
        }
        
        if (print.containsKey("mc_percent")) {
            printerStatus.progress = print["mc_percent"];
        }
        
        // Check for timelapse mode in ipcam object
        if (print.containsKey("ipcam")) {
            JsonObject ipcam = print["ipcam"];
            if (ipcam.containsKey("timelapse")) {
                String timelapse_str = ipcam["timelapse"].as<String>();
                bool new_timelapse_state = (timelapse_str == "enable");
                
                // Log timelapse state changes
                if (new_timelapse_state != timelapse_active) {
                    logPrintln("=== TIMELAPSE STATE CHANGE ===");
                    logPrintln("Timelapse: " + String(timelapse_active ? "ON" : "OFF") + " -> " + String(new_timelapse_state ? "ON" : "OFF"));
                    logPrintln("============================");
                    timelapse_active = new_timelapse_state;
                }
            }
        }
        
        if (print.containsKey("gcode_state")) {
            String old_state = printerStatus.gcode_state;
            String new_state = print["gcode_state"].as<String>();
            
            // If a new print starts (RUNNING/PREPARE), unlock the idle state
            if (new_state == "RUNNING" || new_state == "PREPARE") {
                idle_state_locked = false;
            }
            
            // Only update gcode_state if not locked in IDLE
            if (!idle_state_locked) {
                printerStatus.gcode_state = new_state;
            }
            
            // Log print state changes
            if (old_state != printerStatus.gcode_state) {
                logPrintln("=== PRINT STATE CHANGE ===");
                logPrintln("From: " + old_state + " -> To: " + printerStatus.gcode_state);
                logPrintln("Progress: " + String(printerStatus.progress) + "%");
                logPrintln("Layer: " + String(printerStatus.layer_num) + "/" + String(printerStatus.total_layer_num));
                logPrintln("========================");
            }
            
            // Clear timelapse state when print ends
            if ((printerStatus.gcode_state == "FINISH" || printerStatus.gcode_state == "IDLE") && timelapse_active) {
                logPrintln("Print ended - clearing timelapse state");
                timelapse_active = false;
            }
            
            // Cancel auto-off timer when a new print starts (RUNNING or PREPARE state)
            if ((printerStatus.gcode_state == "RUNNING" || printerStatus.gcode_state == "PREPARE") && 
                (old_state != "RUNNING" && old_state != "PREPARE") && auto_off_pending) {
                auto_off_pending = false;
                logPrintln("Auto-off timer cancelled: New print started");
            }
            
            // Start auto-off timer when print finishes (if in PRINTER mode and timer enabled)
            if (printerStatus.gcode_state == "FINISH" && old_state != "FINISH" && 
                auto_off_minutes > 0 && !auto_off_pending && currentMode == MODE_PRINTER) {
                auto_off_pending = true;
                lights_on_time = millis();
                logPrintln("Print complete - auto-off timer started: " + String(auto_off_minutes) + " minutes");
            }
        }
        
        // mc_print_stage is usually a string like "printing", "heating", etc.
        if (print.containsKey("mc_print_stage")) {
            printerStatus.mc_print_stage = print["mc_print_stage"].as<String>();
        }
        
        // print_real_action is usually a numeric code
        if (print.containsKey("print_real_action")) {
            printerStatus.print_real_action = String(print["print_real_action"].as<int>());
        }
        
        // Get layer information for first layer detection
        if (print.containsKey("layer_num")) {
            printerStatus.layer_num = print["layer_num"];
        }
        if (print.containsKey("total_layer_num")) {
            printerStatus.total_layer_num = print["total_layer_num"];
        }
        
        yield(); // Yield during processing
        
        // Capture additional fields to detect true idle state
        if (print.containsKey("gcode_file")) {
            printerStatus.gcode_file = print["gcode_file"].as<String>();
        }
        if (print.containsKey("subtask_name")) {
            printerStatus.subtask_name = print["subtask_name"].as<String>();
        }
        if (print.containsKey("print_error")) {
            printerStatus.print_error = print["print_error"];
        }
        
        yield(); // Yield after field extraction
        
        // Smart FINISH->IDLE and FAILED->IDLE transition using mc_print_stage
        // mc_print_stage: 1 = idle/no active print, 2 = printing/preparing
        // When printer is in FINISH/FAILED state but mc_print_stage returns to 1, it's truly idle
        if ((printerStatus.gcode_state == "FINISH" || printerStatus.gcode_state == "FAILED") && 
            printerStatus.mc_print_stage == "1" && 
            !idle_state_locked) {
            logPrintln("=== AUTO IDLE DETECTION ===");
            logPrintln(printerStatus.gcode_state + " state with Print Stage=1 (no active job) - transitioning to IDLE");
            logPrintln("Progress: " + String(printerStatus.progress) + "%, Layer: " + String(printerStatus.layer_num) + "/" + String(printerStatus.total_layer_num));
            logPrintln("Locking IDLE state to prevent MQTT overwrite");
            logPrintln("=========================");
            printerStatus.gcode_state = "IDLE";
            idle_state_locked = true; // Lock IDLE state until next print starts
        }
    }
    
    // Parse temperature data - handle multiple field name variations
    if (doc.containsKey("print")) {
        JsonObject print = doc["print"];
        
        // Bed temperature - actual current temperature
        if (print.containsKey("bed_temper")) {
            printerStatus.bed_temp = print["bed_temper"].as<float>();
            logPrintln("Bed temp from print.bed_temper: " + String(printerStatus.bed_temp));
        }
        
        // Nozzle temperature - actual current temperature
        if (print.containsKey("nozzle_temper")) {
            printerStatus.nozzle_temp = print["nozzle_temper"].as<float>();
            logPrintln("Nozzle temp from print.nozzle_temper: " + String(printerStatus.nozzle_temp));
        }
    }
    
    // Legacy support for temp object (if it exists in some firmware versions)
    if (doc.containsKey("temp")) {
        JsonObject temp = doc["temp"];
        if (temp.containsKey("bed_temper") && printerStatus.bed_temp == 0.0) {
            printerStatus.bed_temp = temp["bed_temper"].as<float>();
        }
        if (temp.containsKey("nozzle_temper") && printerStatus.nozzle_temp == 0.0) {
            printerStatus.nozzle_temp = temp["nozzle_temper"].as<float>();
        }
    }
    
    // Show key printer status when available with temperature info
    if (doc.containsKey("print")) {
        JsonObject print = doc["print"];
        if (print.containsKey("gcode_state")) {
            Serial.printf("State: %s", print["gcode_state"].as<String>().c_str());
        }
        if (print.containsKey("layer_num") && print.containsKey("total_layer_num")) {
            Serial.printf(", Layer: %d/%d", print["layer_num"].as<int>(), print["total_layer_num"].as<int>());
        }
        if (print.containsKey("mc_print_stage")) {
            Serial.printf(", Stage: %s", print["mc_print_stage"].as<String>().c_str());
        }
        if (print.containsKey("stg_cur")) {
            Serial.printf(", StgCur: %d", print["stg_cur"].as<int>());
        }
        Serial.println();
    }
    
    // Show temperature data when available
    if (doc.containsKey("temp")) {
        JsonObject temp = doc["temp"];
        bool has_temp = false;
        if (temp.containsKey("bed_temper") || temp.containsKey("bed_temp")) {
            Serial.printf("Temps: Bed=%.1f°C", printerStatus.bed_temp);
            has_temp = true;
        }
        if (temp.containsKey("nozzle_temper") || temp.containsKey("nozzle_temp")) {
            if (has_temp) Serial.printf(", ");
            else Serial.printf("Temps: ");
            Serial.printf("Nozzle=%.1f°C", printerStatus.nozzle_temp);
            has_temp = true;
        }
        if (has_temp) Serial.println();
    }
    
    // Check for door events using proper bit 23 (0x00800000) detection
    // Note: Don't reset door_detected here - it's a global variable that should maintain state between messages
    // Only update it when home_flag is actually present in the MQTT message
    static bool door_detected = false;
    
    // Primary method: Check bit 23 in home_flag (standard Bambu Lab door sensor bit)
    // home_flag is typically inside the "print" object
    if (doc.containsKey("print") && doc["print"].containsKey("home_flag")) {
        long home_flag = doc["print"]["home_flag"];
        
        // Track home_flag changes for door detection
        if (!home_flag_initialized || home_flag != last_home_flag) {
            if (!home_flag_initialized) {
                Serial.printf("Home flag initialized: 0x%08X\n", (unsigned long)home_flag);
                home_flag_initialized = true;
            } else {
                // Check specifically bit 23 (door bit)
                unsigned long old_unsigned = (unsigned long)last_home_flag;
                unsigned long new_unsigned = (unsigned long)home_flag;
                bool old_door_bit = (old_unsigned & 0x00800000UL) != 0;
                bool new_door_bit = (new_unsigned & 0x00800000UL) != 0;
                if (old_door_bit != new_door_bit) {
                    Serial.printf("DOOR %s (home_flag: 0x%08X)\n",
                                 new_door_bit ? "OPENED" : "CLOSED", new_unsigned);
                }
            }
            last_home_flag = home_flag;
        }
        
        const unsigned long DOOR_OPEN_BIT = 0x00800000UL; // Bit 23 (24th bit, zero-indexed)
        
        // Convert to unsigned for proper bit operations
        unsigned long home_flag_unsigned = (unsigned long)home_flag;
        
        // Update door_detected based on bit state
        door_detected = (home_flag_unsigned & DOOR_OPEN_BIT) != 0;
    } else if (doc.containsKey("home_flag")) {
        // Fallback: check at root level
        long home_flag = doc["home_flag"];
        
        // Track root level home_flag changes
        if (!home_flag_initialized || home_flag != last_home_flag) {
            if (!home_flag_initialized) {
                Serial.printf("Home flag initialized (root): 0x%08X - Waiting for fresh update...\n", (unsigned long)home_flag);
                home_flag_initialized = true;
            } else {
                // This is a REAL update (not first stale value)
                home_flag_update_count++;
                
                // Check door bit changes (bit 23: 1=CLOSED, 0=OPEN - inverted logic)
                unsigned long old_unsigned = (unsigned long)last_home_flag;
                unsigned long new_unsigned = (unsigned long)home_flag;
                bool old_door_bit = (old_unsigned & 0x00800000UL) != 0;
                bool new_door_bit = (new_unsigned & 0x00800000UL) != 0;
                if (old_door_bit != new_door_bit) {
                    // Inverted: bit SET = CLOSED, bit CLEAR = OPEN
                    Serial.printf("DOOR %s (home_flag: 0x%08X)\n",
                                 new_door_bit ? "CLOSED" : "OPENED", new_unsigned);
                }
            }
            last_home_flag = home_flag;
        }
        
        // Only trust door detection after we've received at least one real update
        if (home_flag_update_count > 0) {
            const unsigned long DOOR_CLOSED_BIT = 0x00800000UL;  // Bit 23: 1=CLOSED, 0=OPEN
            unsigned long home_flag_unsigned = (unsigned long)home_flag;
            
            // Update door_detected: Door is OPEN when bit is CLEAR (inverted logic)
            door_detected = !(home_flag_unsigned & DOOR_CLOSED_BIT);
        }
    }
    
    // Combine automatic detection with manual trigger
    bool prev_door_state = door_is_open;
    door_is_open = door_detected || manual_door_trigger;
    bool door_just_closed = prev_door_state && !door_is_open;
    
    // Log door state changes with detailed info
    if (door_is_open != prev_door_state) {
        String doorSource = "";
        if (door_detected && manual_door_trigger) {
            doorSource = " (Auto + Manual)";
        } else if (door_detected) {
            doorSource = " (Auto Detection)";
        } else if (manual_door_trigger) {
            doorSource = " (Manual Override)";
        }
        
        logPrintln("=== DOOR STATE CHANGE ===" + doorSource);
        logPrintln("Door: " + String(door_is_open ? "OPEN" : "CLOSED"));
        logPrintln("Door Lights Enabled: " + String(door_open_lights_enabled ? "YES" : "NO"));
        logPrintln("Current Mode: " + String(
            currentMode == MODE_AUTO ? "AUTO" :
            currentMode == MODE_MANUAL ? "MANUAL" :
            currentMode == MODE_PRINTER ? "PRINTER" : "OFF"
        ));
        
        // If door opens and mode is OFF (from auto-off), restore previous mode
        if (door_is_open && currentMode == MODE_OFF && door_open_lights_enabled) {
            logPrintln("Restoring mode from AUTO-OFF: " + String(
                mode_before_auto_off == MODE_AUTO ? "AUTO" :
                mode_before_auto_off == MODE_MANUAL ? "MANUAL" :
                mode_before_auto_off == MODE_PRINTER ? "PRINTER" : "OFF"
            ));
            currentMode = mode_before_auto_off;
            
            // Restore chamber light if it was on before auto-off
            if (chamber_light_sync_enabled && chamber_light_was_on_before_auto_off && mqttClient.connected()) {
                logPrintln("Restoring chamber light (synced)");
                setChamberLight(true);
                chamber_light_was_on_before_auto_off = false;
            }
        }
        
        logPrintln("========================");
    }
    
    // Transition from FINISHED to IDLE when door closes (after user retrieves print)
    if (!door_is_open && prev_door_state && printerStatus.gcode_state == "FINISH") {
        logPrintln("=== PRINT RETRIEVED ===");
        logPrintln("Door closed after FINISH state - transitioning to IDLE");
        printerStatus.gcode_state = "IDLE";
        logPrintln("======================");
    }
    
    // Start auto-off timer if door opens and lights turn on (if timer enabled and not already running)
    if (door_is_open && !prev_door_state && auto_off_minutes > 0 && 
        currentMode == MODE_PRINTER && door_open_lights_enabled) {
        if (!auto_off_pending) {
            auto_off_pending = true;
            lights_on_time = millis();
            logPrintln("Door opened - auto-off timer started: " + String(auto_off_minutes) + " minutes");
        } else {
            // If timer already running, restart it
            lights_on_time = millis();
            logPrintln("Door opened - auto-off timer restarted");
        }
    }
    
    // *** LiDAR SCANNING DETECTION ***
    // Detect when the printer is performing LiDAR scans (typically after first layer)
    bool new_lidar_scanning = false;
    
    // Check for LiDAR scanning conditions
    if (printerStatus.mc_print_stage == "scanning" || 
        printerStatus.mc_print_stage == "first_layer_scan" ||
        printerStatus.mc_print_stage == "auto_bed_leveling" ||
        printerStatus.print_real_action == "scanning" ||
        printerStatus.print_real_action == "lidar_scan" ||
        printerStatus.print_real_action == "first_layer_inspect" ||
        (printerStatus.layer_num == 1 && 
         (printerStatus.mc_print_stage.indexOf("inspect") >= 0 || 
          printerStatus.mc_print_stage.indexOf("scan") >= 0)) ||
        printerStatus.mc_print_stage.indexOf("bed_leveling") >= 0 ||
        printerStatus.mc_print_stage.indexOf("calibrat") >= 0 ||
        printerStatus.print_real_action.indexOf("bed_leveling") >= 0 ||
        printerStatus.print_real_action.indexOf("calibrat") >= 0) {
        new_lidar_scanning = true;
    }
    
    // Update LiDAR scanning state
    if (new_lidar_scanning != lidar_scanning) {
        lidar_scanning = new_lidar_scanning;
        if (lidar_scanning) {
            logPrintln("=== LiDAR SCAN STARTED ===");
            logPrintln("Stage: " + printerStatus.mc_print_stage);
            logPrintln("Action: " + printerStatus.print_real_action);
            logPrintln("Layer: " + String(printerStatus.layer_num));
            logPrintln("Lights: " + String(lidar_lights_off_enabled ? "OFF (pause enabled)" : "STAYING ON (pause disabled)"));
            logPrintln("========================");
        } else {
            logPrintln("=== LiDAR SCAN ENDED - Lights Restored ===");
        }
    }
    
    yield(); // Final yield before LED update
    
    // Only update LEDs based on printer state if in PRINTER mode
    // Skip updates when door is open (to prevent jogging from changing LED color)
    // Force update when door closes to immediately restore LEDs to printer state
    if (currentMode == MODE_PRINTER && (!door_is_open || door_just_closed)) {
        updatePrinterLEDs();
    }
    
    yield(); // Yield after processing complete
}

// Apply LED effect based on behavior configuration (declaration in led_effects.h)
void applyEffect(PrinterStateBehavior& behavior, int progress) {
    uint8_t r = (behavior.color.r * behavior.brightness) / 100;
    uint8_t g = (behavior.color.g * behavior.brightness) / 100;
    uint8_t b = (behavior.color.b * behavior.brightness) / 100;
    
    if (behavior.effect == "solid") {
        setAllLEDs(r, g, b);
    } 
    else if (behavior.effect == "blink") {
        static unsigned long lastBlink = 0;
        static bool blinkState = false;
        if (millis() - lastBlink > 500) {
            blinkState = !blinkState;
            lastBlink = millis();
        }
        if (blinkState) {
            setAllLEDs(r, g, b);
        } else {
            clearAllLEDs();
        }
    }
    else if (behavior.effect == "breathe") {
        static unsigned long lastBreath = 0;
        static float breathPhase = 0;
        if (millis() - lastBreath > 30) {
            breathPhase += 0.05;
            if (breathPhase > 6.28) breathPhase = 0;
            lastBreath = millis();
        }
        float brightness = (sin(breathPhase) + 1.0) / 2.0;  // 0.0 to 1.0
        setAllLEDs(r * brightness, g * brightness, b * brightness);
    }
    else if (behavior.effect == "pulse") {
        static unsigned long lastPulse = 0;
        static bool pulseOn = false;
        static float pulsePhase = 0;
        
        if (pulseOn) {
            // Quick fade in/out pulse
            if (millis() - lastPulse > 15) {
                pulsePhase += 0.15;
                if (pulsePhase > 3.14) {  // Half sine wave (0 to π)
                    pulsePhase = 0;
                    pulseOn = false;
                    lastPulse = millis();
                }
            }
            float brightness = sin(pulsePhase);  // 0.0 to 1.0
            setAllLEDs(r * brightness, g * brightness, b * brightness);
        } else {
            // Off period between pulses
            setAllLEDs(0, 0, 0);
            if (millis() - lastPulse > 1500) {  // 1.5 second pause between pulses
                pulseOn = true;
                pulsePhase = 0;
                lastPulse = millis();
            }
        }
    }
    else if (behavior.effect == "progress" && progress >= 0) {
        // Progress bar effect
        if (progress < 0) progress = 0;
        if (progress > 100) progress = 100;
        
        int ledsToLight = (progress * num_leds) / 100;
        clearAllLEDs();
        
        // Light up completed portion
        for (int i = 0; i < ledsToLight && i < num_leds; i++) {
            setLED(i, r, g, b);
        }
        
        // Show leading edge in brighter color
        if (progress >= 1 && progress < 100 && ledsToLight < num_leds) {
            setLED(ledsToLight, behavior.color.r, behavior.color.g, behavior.color.b);  // Full brightness leading edge
        }
    }
    else if (behavior.effect == "rainbow") {
        // Rainbow cycle effect
        static unsigned long lastRainbow = 0;
        static int rainbowOffset = 0;
        if (millis() - lastRainbow > 50) {  // Update every 50ms
            rainbowOffset = (rainbowOffset + 1) % 256;
            lastRainbow = millis();
        }
        
        for (int i = 0; i < num_leds; i++) {
            int hue = (rainbowOffset + (i * 256 / num_leds)) % 256;
            
            // HSV to RGB conversion (simplified)
            int segment = hue / 43;  // 0-5
            int fraction = (hue % 43) * 6;  // 0-255
            
            int p = 0;
            int q = (255 * (255 - fraction)) / 255;
            int t = (255 * fraction) / 255;
            
            int rr, gg, bb;
            switch(segment) {
                case 0: rr = 255; gg = t;   bb = p;   break;
                case 1: rr = q;   gg = 255; bb = p;   break;
                case 2: rr = p;   gg = 255; bb = t;   break;
                case 3: rr = p;   gg = q;   bb = 255; break;
                case 4: rr = t;   gg = p;   bb = 255; break;
                default: rr = 255; gg = p;   bb = q;   break;
            }
            
            // Apply brightness scaling
            rr = (rr * behavior.brightness) / 100;
            gg = (gg * behavior.brightness) / 100;
            bb = (bb * behavior.brightness) / 100;
            
            setLED(i, rr, gg, bb);
        }
    }
    else {
        // Default to solid if unknown effect
        setAllLEDs(r, g, b);
    }
}

void updatePrinterLEDs() {
    if (currentMode != MODE_PRINTER) return;
    
    // Door open has priority - skip printer LED updates when door is open
    // IMPORTANT: This prevents LED state from updating, but door lights handle the override
    if (door_open_lights_enabled && door_is_open) {
        // Don't return immediately - let door lights in main loop handle this
        // This prevents state from getting stuck when door closes
        return;
    }
    
    // Priority 1: LiDAR scanning - turn off lights to avoid interference (if enabled)
    if (lidar_lights_off_enabled && lidar_scanning) {
        clearAllLEDs();
        updateLEDs();
        return;
    }
    
    // Track LED mode for change detection
    static uint8_t last_led_mode = 0; // 0=none, 1=white, 2=normal
    static String last_gcode_state = "";
    static bool finish_effect_logged = false;
    uint8_t current_led_mode = 0;
    
    // Log state changes for debugging
    if (printerStatus.gcode_state != last_gcode_state) {
        logPrintln(">>> PRINTER STATE CHANGE: " + last_gcode_state + " -> " + printerStatus.gcode_state + " <<<");
        last_gcode_state = printerStatus.gcode_state;
        finish_effect_logged = false; // Reset when state changes
        
        // Publish state change to Home Assistant
        publishHAState();
    }
    
    // Priority 2: Timelapse mode - force white lights during printing for consistent lighting
    // Only activate if BOTH the setting is enabled AND timelapse is actually active in the print
    if (timelapse_white_lights_enabled && timelapse_active && (printerStatus.gcode_state == "RUNNING" || printerStatus.gcode_state == "PREPARE")) {
        current_led_mode = 1; // White mode
        if (last_led_mode != 1) {
            logPrintln(">>> LED MODE CHANGE: Timelapse WHITE lights active <<<");
            last_led_mode = 1;
        }
        
        setAllLEDs(255, 255, 255); // Full white for timelapse
        updateLEDs();
        
        // Keep chamber light on if sync is enabled (always on for timelapse white mode)
        if (chamber_light_sync_enabled) {
            setChamberLight(true);
        }
        
        // Prevent auto-off during timelapse recording
        if (auto_off_pending) {
            auto_off_pending = false;
            logPrintln("Auto-off cancelled: Timelapse recording active");
        }
        
        return;
    }
    
    // Handle timelapse active but white lights disabled - keep chamber on only if using white printing color
    if (timelapse_active && (printerStatus.gcode_state == "RUNNING" || printerStatus.gcode_state == "PREPARE")) {
        current_led_mode = 2; // Normal mode
        if (last_led_mode != 2) {
            logPrintln(">>> LED MODE CHANGE: Timelapse NORMAL lights (using printer status colors) <<<");
            last_led_mode = 2;
        }
        
        // Keep chamber light on if sync is enabled AND printing color is white (255,255,255)
        // This prevents chamber light from washing out custom printing colors
        if (chamber_light_sync_enabled && 
            behavior_printing.color.r == 255 && 
            behavior_printing.color.g == 255 && 
            behavior_printing.color.b == 255) {
            setChamberLight(true);
        }
        
        // Prevent auto-off during timelapse recording
        if (auto_off_pending) {
            auto_off_pending = false;
            logPrintln("Auto-off cancelled: Timelapse recording active (white lights disabled)");
        }
        // Continue to normal printer status logic below
    }
    
    // If we're no longer in timelapse mode, reset tracking
    if (current_led_mode == 0 && last_led_mode != 0) {
        logPrintln(">>> LED MODE CHANGE: Exited timelapse mode <<<");
        last_led_mode = 0;
    }
    
    // Priority 3: Printer state-based colors with configurable effects
    if (!printerStatus.online || millis() - printerStatus.lastUpdate > 60000) {
        // Offline/Error - use error behavior
        applyEffect(behavior_error);
    } else if (printerStatus.gcode_state == "IDLE") {
        applyEffect(behavior_idle);
    } else if (printerStatus.gcode_state == "RUNNING" || printerStatus.gcode_state == "PREPARE") {
        // Check stage number to differentiate heating from actual printing
        // Stage 2 = HEATBED_PREHEATING, Stage 3 = HEATING_HOTEND, etc.
        // Stage 14+ = actual printing stages
        int stageNum = printerStatus.stage.toInt();
        if (stageNum > 0 && stageNum < 10 && printerStatus.progress == 0) {
            // Heating/preparation stages (stage 1-9) with 0% progress = heating phase
            applyEffect(behavior_heating);
        } else {
            // Actually printing
            applyEffect(behavior_printing, printerStatus.progress);
        }
    } else if (printerStatus.gcode_state == "PAUSE") {
        applyEffect(behavior_pause, printerStatus.progress);
    } else if (printerStatus.gcode_state == "FINISH") {
        if (!finish_effect_logged) {
            logPrintln("=== APPLYING FINISH STATE ===");
            logPrintln("Effect: " + behavior_finish.effect);
            logPrintln("Color: RGB(" + String(behavior_finish.color.r) + "," + String(behavior_finish.color.g) + "," + String(behavior_finish.color.b) + ")");
            logPrintln("Brightness: " + String(behavior_finish.brightness) + "%");
            logPrintln("==============================");
            finish_effect_logged = true;
        }
        applyEffect(behavior_finish);
    } else if (printerStatus.gcode_state == "FAILED") {
        // FAILED state (cancelled print) - treat as idle since it's not a real error
        // Real errors would have print_error != 0 or mc_print_error_code != "0"
        applyEffect(behavior_idle);
    } else {
        // Unknown state - use error behavior
        applyEffect(behavior_error);
    }
    
    // Manage chamber light based on printing color
    // Turn ON for white (255,255,255), turn OFF for any other color
    if (chamber_light_sync_enabled && 
        (printerStatus.gcode_state == "RUNNING" || printerStatus.gcode_state == "PREPARE")) {
        if (behavior_printing.color.r == 255 && 
            behavior_printing.color.g == 255 && 
            behavior_printing.color.b == 255) {
            setChamberLight(true);  // White printing color - turn on chamber light
        } else {
            setChamberLight(false); // Non-white printing color - turn off chamber light
        }
    }
    
    updateLEDs();
}

// espMqttClient handles SSL internally, no separate client setup needed

bool connectMQTT() {
    logPrintln("=== MQTT Connection Debug ===");
    logPrintln("MQTT Server: " + mqtt_server);
    logPrintln("MQTT Port: " + String(mqtt_port));
    logPrintln("MQTT SSL: " + String(mqtt_use_ssl ? "YES" : "NO"));
    logPrintln("MQTT Skip Cert: " + String(mqtt_skip_cert_check ? "YES" : "NO"));
    logPrintln("MQTT Username: " + String(MQTT_USERNAME));
    logPrintln("Device Serial: " + device_serial);
    logPrintln("WiFi Status: " + String(WiFi.status() == WL_CONNECTED ? "Connected" : "Disconnected"));
    logPrintln("WiFi IP: " + WiFi.localIP().toString());
    
    // Set up espMqttClientSecure configuration  
    mqttClient.onMessage(onMqttMessage);
    
    // Configure SSL/TLS - espMqttClientSecure is always secure
    if (mqtt_skip_cert_check) {
        logPrintln("WARNING: Skipping SSL certificate verification");
        mqttClient.setInsecure();  // Skip certificate verification for Bambu Lab
    }
    
    mqttClient.setServer(mqtt_server.c_str(), mqtt_port);
    mqttClient.setCredentials(MQTT_USERNAME, mqtt_password.c_str());
    mqttClient.setKeepAlive(60);
    
    logPrintln("Connecting to MQTT: " + mqtt_server + ":" + String(mqtt_port));
    
    // Use truly unique client ID to avoid conflicts
    String clientId = String(random(100000, 999999)) + "_" + String(millis());
    logPrintln("Client ID: " + clientId);
    mqttClient.setClientId(clientId.c_str());
    
    mqttClient.connect();
    
    // Wait for connection with timeout
    int connectionAttempts = 0;
    const int maxAttempts = 30; // 15 seconds timeout
    while (!mqttClient.connected() && connectionAttempts < maxAttempts) {
        delay(500);
        connectionAttempts++;
        yield();
    }
    
    if (mqttClient.connected()) {
        logPrintln("MQTT connected successfully!");
        
        // Subscribe to printer status topic
        String statusTopic = "device/" + device_serial + "/report";
        mqttClient.subscribe(statusTopic.c_str(), 0);  // QOS 0
        logPrintln("Subscribed to: " + statusTopic);
        
        // DEBUGGING: Subscribe to ALL device topics to see what's actually being published
        mqttClient.subscribe("device/+/report", 0);  // QOS 0
        logPrintln("DEBUG: Subscribed to device/+/report (wildcard)");
        
        mqttClient.subscribe("device/+/info", 0);  // QOS 0
        logPrintln("DEBUG: Subscribed to device/+/info (wildcard)");
        
        // Subscribe to even broader pattern to catch everything
        mqttClient.subscribe("device/#", 0);  // QOS 0
        logPrintln("DEBUG: Subscribed to device/# (all device topics)");
        
        // ENHANCED DEBUGGING: Try subscribing to ALL topics to see what's available
        logPrintln("DEBUG: Subscribing to ALL MQTT topics for debugging...");
        mqttClient.subscribe("#", 0);  // Subscribe to EVERYTHING, QOS 0
        logPrintln("DEBUG: Subscribed to # (ALL TOPICS)");
        
        // Also try some common Bambu Lab topic patterns
        mqttClient.subscribe("bambulabs/+/report", 0);  // QOS 0
        logPrintln("DEBUG: Subscribed to bambulabs/+/report");
        
        mqttClient.subscribe("bambu/+/report", 0);  // QOS 0
        logPrintln("DEBUG: Subscribed to bambu/+/report");
        
        // CALLBACK TEST: Subscribe to test topic and publish test message
        String testTopic = "device/" + device_serial + "/test";
        mqttClient.subscribe(testTopic.c_str(), 0);  // QOS 0
        Serial.printf("DEBUG: Subscribed to test topic: %s\n", testTopic.c_str());
        
        Serial.println("DEBUG: Publishing test message to verify callback...");
        mqttClient.publish(testTopic.c_str(), 0, false, "{\"test\":\"callback_verification\",\"home_flag\":-1234567}");  // QOS 0, no retain
        delay(100); // Give time for callback
        Serial.println("DEBUG: Test message published, callback should have triggered");
        
        // Send connection confirmation
        setAllLEDs(0, 255, 0); // Green
        updateLEDs();
        delay(500); // Reduced delay to keep interface responsive
        yield(); // Yield to keep web server responsive
        
        return true;
    } else {
        Serial.println("MQTT connection failed!");
        Serial.println("Check your MQTT server, credentials, and network settings.");
        yield(); // Yield after failed connection attempt
        
        // Red blink for MQTT failure
        setAllLEDs(255, 0, 0);
        updateLEDs();
        delay(300); // Reduced delay to keep interface responsive
        yield(); // Yield to keep web server responsive
        
        return false;
    }
}

// Home Assistant MQTT Discovery helpers
String getDeviceId() {
    uint32_t chipId = 0;
    for(int i=0; i<17; i=i+8) {
        chipId |= ((ESP.getEfuseMac() >> (40 - i)) & 0xff) << i;
    }
    return String(chipId, HEX);
}

void publishHADiscovery() {
    if (!haMqttClient.connected() || !ha_mqtt_enabled) {
        return;
    }
    
    String deviceId = "bambu_lights_" + getDeviceId();
    String baseTopic = "homeassistant/sensor/" + deviceId;
    
    // State topic base from device name
    String stateTopicBase = ha_device_name;
    stateTopicBase.replace(" ", "_");
    
    // Device info shared by all sensors
    String deviceJson = "\"device\":{\"identifiers\":[\"" + deviceId + "\"],"
                       "\"name\":\"" + ha_device_name + "\","
                       "\"manufacturer\":\"Bambu Lights\","
                       "\"model\":\"ESP32 LED Controller\","
                       "\"sw_version\":\"1.0\"}";
    
    // State sensor
    String stateConfig = "{\"name\":\"Printer State\","
                        "\"state_topic\":\"" + stateTopicBase + "/state\","
                        "\"unique_id\":\"" + deviceId + "_state\","
                        "\"icon\":\"mdi:printer-3d\","
                        + deviceJson + "}";
    haMqttClient.publish((baseTopic + "_state/config").c_str(), 0, true, stateConfig.c_str());
    
    // Progress sensor
    String progressConfig = "{\"name\":\"Print Progress\","
                           "\"state_topic\":\"" + stateTopicBase + "/progress\","
                           "\"unique_id\":\"" + deviceId + "_progress\","
                           "\"unit_of_measurement\":\"%\","
                           "\"icon\":\"mdi:progress-clock\","
                           + deviceJson + "}";
    haMqttClient.publish((baseTopic + "_progress/config").c_str(), 0, true, progressConfig.c_str());
    
    // Bed temperature sensor
    String bedTempConfig = "{\"name\":\"Bed Temperature\","
                          "\"state_topic\":\"" + stateTopicBase + "/bed_temp\","
                          "\"unique_id\":\"" + deviceId + "_bed_temp\","
                          "\"unit_of_measurement\":\"°C\","
                          "\"device_class\":\"temperature\","
                          "\"icon\":\"mdi:thermometer\","
                          + deviceJson + "}";
    haMqttClient.publish((baseTopic + "_bed_temp/config").c_str(), 0, true, bedTempConfig.c_str());
    
    // Nozzle temperature sensor
    String nozzleTempConfig = "{\"name\":\"Nozzle Temperature\","
                             "\"state_topic\":\"" + stateTopicBase + "/nozzle_temp\","
                             "\"unique_id\":\"" + deviceId + "_nozzle_temp\","
                             "\"unit_of_measurement\":\"°C\","
                             "\"device_class\":\"temperature\","
                             "\"icon\":\"mdi:printer-3d-nozzle\","
                             + deviceJson + "}";
    haMqttClient.publish((baseTopic + "_nozzle_temp/config").c_str(), 0, true, nozzleTempConfig.c_str());
    
    // Layer sensor
    String layerConfig = "{\"name\":\"Current Layer\","
                        "\"state_topic\":\"" + stateTopicBase + "/layer\","
                        "\"unique_id\":\"" + deviceId + "_layer\","
                        "\"icon\":\"mdi:layers\","
                        + deviceJson + "}";
    haMqttClient.publish((baseTopic + "_layer/config").c_str(), 0, true, layerConfig.c_str());
    
    // Filename sensor
    String filenameConfig = "{\"name\":\"Current File\","
                           "\"state_topic\":\"" + stateTopicBase + "/filename\","
                           "\"unique_id\":\"" + deviceId + "_filename\","
                           "\"icon\":\"mdi:file-document\","
                           + deviceJson + "}";
    haMqttClient.publish((baseTopic + "_filename/config").c_str(), 0, true, filenameConfig.c_str());
    
    // Binary sensor for printing status
    String binaryBaseTopic = "homeassistant/binary_sensor/" + deviceId;
    String printingConfig = "{\"name\":\"Printing\","
                           "\"state_topic\":\"" + stateTopicBase + "/printing\","
                           "\"unique_id\":\"" + deviceId + "_printing\","
                           "\"device_class\":\"running\","
                           "\"payload_on\":\"ON\","
                           "\"payload_off\":\"OFF\","
                           + deviceJson + "}";
    haMqttClient.publish((binaryBaseTopic + "_printing/config").c_str(), 0, true, printingConfig.c_str());
    
    logPrintln("HA: Published MQTT Discovery messages");
}

void publishHAState() {
    if (!haMqttClient.connected() || !ha_mqtt_enabled) {
        return;
    }
    
    static unsigned long lastPublish = 0;
    static String lastState = "";
    static int lastProgress = -1;
    static bool firstPublish = true;
    
    // Throttle updates to once per second max (but allow first publish)
    if (!firstPublish && millis() - lastPublish < 1000) {
        return;
    }
    
    // Force telemetry update every 5 minutes (300000ms)
    bool forceUpdate = (millis() - lastPublish >= 300000);
    
    // Publish if state/progress changed, first publish, or 5 minutes elapsed
    if (!firstPublish && !forceUpdate && printerStatus.gcode_state == lastState && printerStatus.progress == lastProgress) {
        return;
    }
    
    firstPublish = false;
    lastPublish = millis();
    lastState = printerStatus.gcode_state;
    lastProgress = printerStatus.progress;
    
    // Build topic base from device name
    String topicBase = ha_device_name;
    topicBase.replace(" ", "_");
    
    // Publish state
    haMqttClient.publish((topicBase + "/state").c_str(), 0, false, printerStatus.gcode_state.c_str());
    
    // Publish progress
    String progressStr = String(printerStatus.progress);
    haMqttClient.publish((topicBase + "/progress").c_str(), 0, false, progressStr.c_str());
    
    // Publish bed temperature
    String bedTempStr = String(printerStatus.bed_temp);
    haMqttClient.publish((topicBase + "/bed_temp").c_str(), 0, false, bedTempStr.c_str());
    
    // Publish nozzle temperature
    String nozzleTempStr = String(printerStatus.nozzle_temp);
    haMqttClient.publish((topicBase + "/nozzle_temp").c_str(), 0, false, nozzleTempStr.c_str());
    
    // Publish layer info
    String layerStr = String(printerStatus.layer_num) + "/" + String(printerStatus.total_layer_num);
    haMqttClient.publish((topicBase + "/layer").c_str(), 0, false, layerStr.c_str());
    
    // Publish filename
    haMqttClient.publish((topicBase + "/filename").c_str(), 0, false, printerStatus.gcode_file.c_str());
    
    // Publish printing binary sensor
    bool isPrinting = (printerStatus.gcode_state == "RUNNING" || printerStatus.gcode_state == "PREPARE");
    haMqttClient.publish((topicBase + "/printing").c_str(), 0, false, isPrinting ? "ON" : "OFF");
    
    logPrintln("HA: Published state update - " + printerStatus.gcode_state + " " + String(printerStatus.progress) + "%");
}

void onHAMqttConnect(bool sessionPresent) {
    logPrintln("HA MQTT connected! Session present: " + String(sessionPresent));
    publishHADiscovery();
    publishHAState(); // Send initial state after discovery
}

bool connectHAMQTT() {
    if (!ha_mqtt_enabled) {
        logPrintln("HA MQTT: Disabled in configuration");
        return false;
    }
    
    logPrintln("=== HA MQTT Connection Debug ===");
    logPrintln("HA MQTT Server: " + ha_mqtt_server);
    logPrintln("HA MQTT Port: " + String(ha_mqtt_port));
    logPrintln("HA MQTT SSL: " + String(ha_mqtt_use_ssl ? "YES" : "NO"));
    logPrintln("HA MQTT Username: " + ha_mqtt_username);
    logPrintln("WiFi Status: " + String(WiFi.status() == WL_CONNECTED ? "Connected" : "Disconnected"));
    
    // Set up callback
    haMqttClient.onConnect(onHAMqttConnect);
    
    // espMqttClient automatically uses non-secure connection
    // For SSL, we would need espMqttClientSecure (not implemented yet)
    
    haMqttClient.setServer(ha_mqtt_server.c_str(), ha_mqtt_port);
    
    if (ha_mqtt_username.length() > 0) {
        haMqttClient.setCredentials(ha_mqtt_username.c_str(), ha_mqtt_password.c_str());
    }
    
    haMqttClient.setKeepAlive(60);
    
    logPrintln("Connecting to HA MQTT: " + ha_mqtt_server + ":" + String(ha_mqtt_port));
    
    // Use unique client ID
    String clientId = "bambu_lights_" + String(random(100000, 999999));
    logPrintln("HA Client ID: " + clientId);
    haMqttClient.setClientId(clientId.c_str());
    
    haMqttClient.connect();
    
    // Wait for connection with timeout
    int connectionAttempts = 0;
    const int maxAttempts = 30; // 15 seconds timeout
    while (!haMqttClient.connected() && connectionAttempts < maxAttempts) {
        delay(500);
        connectionAttempts++;
        yield();
    }
    
    if (haMqttClient.connected()) {
        logPrintln("HA MQTT connected successfully!");
        return true;
    } else {
        logPrintln("HA MQTT connection failed!");
        logPrintln("Check your HA MQTT broker settings.");
        return false;
    }
}
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
void loop() {
    static unsigned long lastUpdate = 0;
    static unsigned long lastWiFiCheck = 0;
    static unsigned long lastMQTTCheck = 0;
    static int colorStep = 0;
    
    // Reset watchdog timer to prevent reboot
    esp_task_wdt_reset();
    
    // Handle Telnet clients
    if (telnetServer.hasClient()) {
        // New client trying to connect
        if (!telnetClient || !telnetClient.connected()) {
            if (telnetClient) telnetClient.stop();
            telnetClient = telnetServer.available();
            telnetClient.flush();
            telnetConnected = true;
            Serial.println("Telnet client connected from " + telnetClient.remoteIP().toString());
            telnetClient.println("=== Bambu LED Controller - Serial Monitor ===");
            telnetClient.println("Connected successfully!");
            telnetClient.println("IP: " + WiFi.localIP().toString());
            telnetClient.println("---");
        } else {
            // Already have a client, reject new connection
            WiFiClient newClient = telnetServer.available();
            newClient.stop();
        }
    }
    
    // Check if Telnet client disconnected
    if (telnetConnected && (!telnetClient || !telnetClient.connected())) {
        Serial.println("Telnet client disconnected");
        telnetConnected = false;
        telnetClient.stop();
    }
    
    // Handle deferred beacon reinitialization (moved from web handler to avoid blocking)
    if (beacon_reinit_pending) {
        beacon_reinit_pending = false;
        logPrintln("Executing deferred beacon reinit...");
        
        // Clean up old beacon
        if (beacon_was_enabled_before_reinit) {
            clearBeaconLEDs();
            updateBeaconLEDs();
            if (beacon_leds != nullptr) {
                free(beacon_leds);
                beacon_leds = nullptr;
            }
            if (beacon_rgbw_leds != nullptr) {
                free(beacon_rgbw_leds);
                beacon_rgbw_leds = nullptr;
            }
            if (beacon_led_data != nullptr) {
                free(beacon_led_data);
                beacon_led_data = nullptr;
            }
            rmt_driver_uninstall(RMT_CHANNEL_1);
            yield(); // Allow web server to process during uninstall
        }
        
        // Initialize new beacon if enabled
        if (beacon_enabled) {
            configureBeaconTiming();
            reallocateBeaconLEDs();
            setupBeaconRMT();
            clearBeaconLEDs();
            updateBeaconLEDs();
            logPrintln("Beacon reinitialized with new settings");
        }
        beacon_was_enabled_before_reinit = false;
    }
    
    // Web server and OTA now handled in dedicated task on Core 0
    
    // Handle MQTT
    if (WiFi.status() == WL_CONNECTED && mqttClient.connected()) {
        // espMqttClient handles message processing automatically, no loop() needed
        yield(); // Give time for background processing
    }
    
    // Handle Home Assistant MQTT
    if (WiFi.status() == WL_CONNECTED && ha_mqtt_enabled) {
        haMqttClient.loop(); // Process MQTT messages (required when UseInternalTask::NO)
        publishHAState(); // Check and publish telemetry updates
        yield(); // Give time for background processing
    }
    
    // Check WiFi status every 30 seconds
    if (millis() - lastWiFiCheck > 30000) {
        lastWiFiCheck = millis();
        
        if (WiFi.status() != WL_CONNECTED) {
            Serial.println("WiFi disconnected! Attempting reconnect...");
            yield();
            connectWiFi();
            yield();
            if (WiFi.status() == WL_CONNECTED) {
                setupWebServer(); // Restart web server after reconnect
                yield();
                connectMQTT(); // Reconnect MQTT
                yield();
                if (ha_mqtt_enabled) {
                    connectHAMQTT(); // Reconnect Home Assistant MQTT
                    yield();
                }
            }
        }
    }
    
    // Check auto-off timer - turns off lights regardless of current mode
    if (auto_off_pending && auto_off_minutes > 0) {
        unsigned long elapsed_minutes = (millis() - lights_on_time) / 60000;
        
        // Log timer status every minute
        static unsigned long last_timer_log = 0;
        if (millis() - last_timer_log > 60000) {
            last_timer_log = millis();
            logPrintln("Auto-off timer: " + String(elapsed_minutes) + "/" + String(auto_off_minutes) + " min elapsed");
        }
        
        if (elapsed_minutes >= auto_off_minutes) {
            // Skip turning off if door is currently open (door lights have priority)
            if (door_open_lights_enabled && door_is_open) {
                logPrintln("Auto-off timer expired but door is open - keeping lights on");
                // Restart timer to check again later
                lights_on_time = millis();
            } else {
                logPrintln("=== AUTO-OFF TIMER EXPIRED ===");
                logPrintln("Timer: " + String(auto_off_minutes) + " minutes");
                logPrintln("Action: Turning OFF lights");
                logPrintln("Previous mode saved for restore");
            
            // Turn off chamber light if sync is enabled
            logPrintln("Chamber Sync Enabled: " + String(chamber_light_sync_enabled ? "YES" : "NO"));
            logPrintln("MQTT Connected: " + String(mqttClient.connected() ? "YES" : "NO"));
            if (chamber_light_sync_enabled && mqttClient.connected()) {
                logPrintln(">>> Turning OFF chamber light (synced)");
                setChamberLight(false);
                chamber_light_was_on_before_auto_off = true; // Assume it was on
            } else {
                if (!chamber_light_sync_enabled) {
                    logPrintln(">>> Chamber sync DISABLED - skipping");
                }
                if (!mqttClient.connected()) {
                    logPrintln(">>> MQTT not connected - skipping");
                }
            }
            
                logPrintln("============================");
                mode_before_auto_off = currentMode; // Save current mode before turning off
                currentMode = MODE_OFF;
                clearAllLEDs();
                updateLEDs();
                auto_off_pending = false;
                lights_on_time = 0;
            }
        }
    }
    
    // Check MQTT connection every 30 seconds (reduced frequency to improve web responsiveness)
    if (millis() - lastMQTTCheck > 30000) {
        lastMQTTCheck = millis();
        
        if (WiFi.status() == WL_CONNECTED && !mqttClient.connected()) {
            Serial.println("MQTT disconnected! Attempting reconnect...");
            yield(); // Yield before attempting connection
            // Non-blocking MQTT connection attempt
            bool connected = connectMQTT();
            Serial.printf("MQTT Reconnect: %s\n", connected ? "OK" : "FAILED");
            yield(); // Yield after MQTT attempt to keep web responsive
        }
    }
    
    // LED updates based on current mode
    // Update every 50ms for smooth color transitions
    if (millis() - lastUpdate > 50) {
        lastUpdate = millis();
        
        static bool doorLightsWereActive = false;
        
        // Priority override: Door open lights (works in any mode)
        if (door_open_lights_enabled && door_is_open) {
            if (!doorLightsWereActive) {
                logPrintln("=== DOOR LIGHTS ACTIVE ===");
                logPrintln("Door Color: RGB(" + String(door_open_color.r) + ", " + String(door_open_color.g) + ", " + String(door_open_color.b) + ")");
                logPrintln("Overriding current mode: " + String(
                    currentMode == MODE_AUTO ? "AUTO" :
                    currentMode == MODE_MANUAL ? "MANUAL" :
                    currentMode == MODE_PRINTER ? "PRINTER" : "OFF"
                ));
                logPrintln("=========================");
                doorLightsWereActive = true;
            }
            setAllLEDs(door_open_color.r, door_open_color.g, door_open_color.b);
            updateLEDs();
        } else if (WiFi.status() == WL_CONNECTED && currentMode == MODE_AUTO) {
            // Door just closed - clear flag
            if (doorLightsWereActive) {
                logPrintln("Door closed - resuming normal mode operation");
                doorLightsWereActive = false;
            }
            
            // Auto mode - smooth color fading with adjustable speed
            // Calculate dynamic fade steps based on speed (1-100)
            // Updates every 50ms, so 20 updates per second
            // Speed controls total fade duration: Speed 1 = 10 seconds, Speed 100 = 1 second
            int cyclesPerColor = 200 - (autoCycleSpeed * 2); // Speed 1 = 200 steps (10s), 100 = 20 steps (1s)
            
            if (fadeStep >= cyclesPerColor) {
                // Time to switch to next color
                currentAutoColor = targetAutoColor;
                fadeStep = 0;
                
                switch (colorStep % 5) {
                    case 0:
                        Serial.println("Auto: Next color -> Soft Blue");
                        targetAutoColor = {0, 0, 128};    // Soft blue
                        break;
                    case 1:
                        Serial.println("Auto: Next color -> Soft Purple");
                        targetAutoColor = {128, 0, 128};  // Soft purple
                        break;
                    case 2:
                        Serial.println("Auto: Next color -> Soft Cyan");
                        targetAutoColor = {0, 128, 128};  // Soft cyan
                        break;
                    case 3:
                        Serial.println("Auto: Next color -> Soft White");
                        targetAutoColor = {100, 100, 100}; // Soft white
                        break;
                    case 4:
                        Serial.println("Auto: Next color -> Soft Green");
                        targetAutoColor = {0, 128, 0};    // Soft green
                        break;
                }
                colorStep++;
            }
            
            // Smooth interpolation between current and target colors
            float progress = (float)fadeStep / cyclesPerColor;
            uint8_t r = currentAutoColor.r + (targetAutoColor.r - currentAutoColor.r) * progress;
            uint8_t g = currentAutoColor.g + (targetAutoColor.g - currentAutoColor.g) * progress;
            uint8_t b = currentAutoColor.b + (targetAutoColor.b - currentAutoColor.b) * progress;
            
            // Apply brightness scaling (0-100%)
            r = (r * autoCycleBrightness) / 100;
            g = (g * autoCycleBrightness) / 100;
            b = (b * autoCycleBrightness) / 100;
            
            setAllLEDs(r, g, b);
            updateLEDs();
            fadeStep++;
        } else if (WiFi.status() != WL_CONNECTED && currentMode == MODE_AUTO) {
            // WiFi disconnected - show red error pattern
            switch (colorStep % 2) {
                case 0:
                    Serial.println("Status: Disconnected - Red blink");
                    setAllLEDs(255, 0, 0);     // Red
                    break;
                case 1:
                    Serial.println("Status: Disconnected - Off");
                    clearAllLEDs();            // Off
                    break;
            }
            updateLEDs();
            colorStep++;
        } else if (currentMode == MODE_PRINTER) {
            // Door just closed - clear flag and force update
            if (doorLightsWereActive) {
                logPrintln("Door closed - resuming normal mode operation");
                doorLightsWereActive = false;
                updatePrinterLEDs(); // Force immediate update to restore printer state
            }
            // Printer mode - always update LEDs, door lights override happens in main loop above
            // This ensures state doesn't get stuck
            else {
                updatePrinterLEDs();
            }
            
            // Check if printer is offline
            if (millis() - printerStatus.lastUpdate > 60000) {
                printerStatus.online = false;
            }
        }
        
        // Update beacon progress if enabled (runs regardless of main LED mode)
        // Throttled to 200ms (5 updates/sec) to prevent blocking web server
        static unsigned long lastBeaconUpdate = 0;
        if (beacon_enabled && beacon_leds && (millis() - lastBeaconUpdate > 50)) {
            lastBeaconUpdate = millis();
            
            // Check if auto-off timer has turned lights off
            if (currentMode == MODE_OFF && mode_before_auto_off != MODE_OFF) {
                // Auto-off timer has expired - turn off beacon
                clearBeaconLEDs();
                updateBeaconLEDs();
            } else if (manual_beacon_trigger) {
                // Manual override - always show at 100%
                updateBeaconProgress(100);
            } else if (printerStatus.gcode_state == "RUNNING" || printerStatus.gcode_state == "PREPARE") {
                // Check if heating (stage 1-9 with 0% progress)
                int stageNum = printerStatus.stage.toInt();
                bool isHeating = (stageNum > 0 && stageNum < 10 && printerStatus.progress == 0);
                
                if (isHeating) {
                    // Temporarily override beacon color to heating color for progress bar animation
                    RGB original_beacon_color = beacon_color;
                    RGB original_climb_color = beacon_climb_color;
                    
                    beacon_color = behavior_heating.color;
                    beacon_climb_color = behavior_heating.color;  // Use heating color for climb too
                    
                    updateBeaconProgress(50);  // Show 50% during heating phase
                    
                    // Restore original colors
                    beacon_color = original_beacon_color;
                    beacon_climb_color = original_climb_color;
                } else {
                    // Normal printing - show actual progress
                    updateBeaconProgress(printerStatus.progress);
                }
            } else if (printerStatus.gcode_state == "IDLE" || printerStatus.gcode_state == "FINISH") {
                // Print finished or idle - show idle state behavior
                // Apply idle color and effect to beacon LEDs
                uint8_t r = (behavior_idle.color.r * behavior_idle.brightness) / 100;
                uint8_t g = (behavior_idle.color.g * behavior_idle.brightness) / 100;
                uint8_t b = (behavior_idle.color.b * behavior_idle.brightness) / 100;
                
                if (behavior_idle.effect == "solid") {
                    // Solid color on all beacon LEDs
                    for (int i = 0; i < beacon_led_count; i++) {
                        setBeaconLED(i, r, g, b);
                    }
                    updateBeaconLEDs();
                } else if (behavior_idle.effect == "blink") {
                    // Blink effect
                    static bool blinkState = false;
                    static unsigned long lastBlink = 0;
                    if (millis() - lastBlink > 500) {
                        blinkState = !blinkState;
                        lastBlink = millis();
                    }
                    for (int i = 0; i < beacon_led_count; i++) {
                        if (blinkState) {
                            setBeaconLED(i, r, g, b);
                        } else {
                            setBeaconLED(i, 0, 0, 0);
                        }
                    }
                    updateBeaconLEDs();
                } else {
                    // For other effects (pulse, rainbow, etc), just show solid
                    for (int i = 0; i < beacon_led_count; i++) {
                        setBeaconLED(i, r, g, b);
                    }
                    updateBeaconLEDs();
                }
            } else if (!printerStatus.online || millis() - printerStatus.lastUpdate > 60000) {
                // Offline/Error state - apply error behavior
                int r = (behavior_error.color.r * behavior_error.brightness) / 100;
                int g = (behavior_error.color.g * behavior_error.brightness) / 100;
                int b = (behavior_error.color.b * behavior_error.brightness) / 100;
                
                if (behavior_error.effect == "solid") {
                    for (int i = 0; i < beacon_led_count; i++) {
                        setBeaconLED(i, r, g, b);
                    }
                    updateBeaconLEDs();
                } else if (behavior_error.effect == "blink") {
                    // Blink effect
                    static bool errorBlinkState = false;
                    static unsigned long lastErrorBlink = 0;
                    if (millis() - lastErrorBlink > 500) {
                        errorBlinkState = !errorBlinkState;
                        lastErrorBlink = millis();
                    }
                    for (int i = 0; i < beacon_led_count; i++) {
                        if (errorBlinkState) {
                            setBeaconLED(i, r, g, b);
                        } else {
                            setBeaconLED(i, 0, 0, 0);
                        }
                    }
                    updateBeaconLEDs();
                } else {
                    // For other effects, just show solid
                    for (int i = 0; i < beacon_led_count; i++) {
                        setBeaconLED(i, r, g, b);
                    }
                    updateBeaconLEDs();
                }
            } else {
                // Unknown state - clear beacon
                clearBeaconLEDs();
                updateBeaconLEDs();
            }
        }
    }
    
    // Network scanning has been removed; manual configuration via web UI is preferred.
}
